mrojas36/CoCoSwitchboard/CoCo1Switchboard/Photos/Capture.PNG

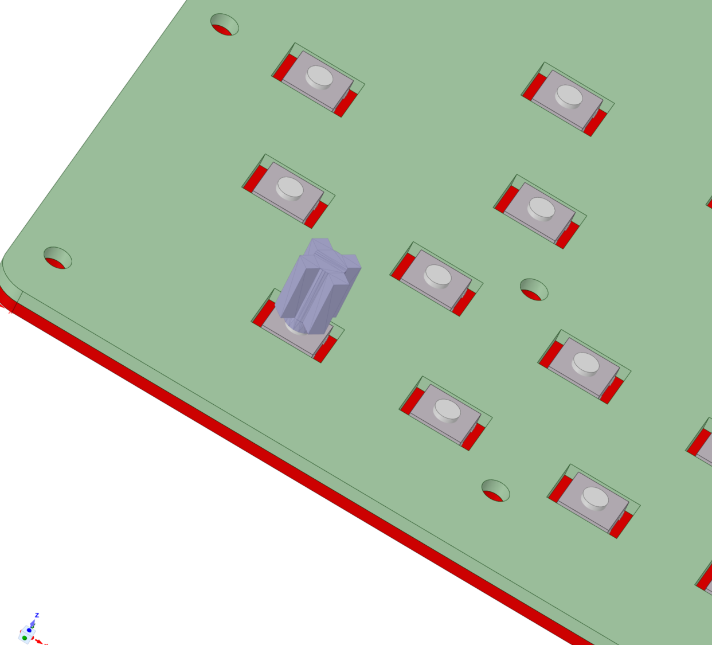
CoCo1Switchboard/Photos/Capture.PNG
