mrojas36/CoCoSwitchboard/CoCo1Switchboard/Photos/Coco1-Keyboard1 (1).JPEG

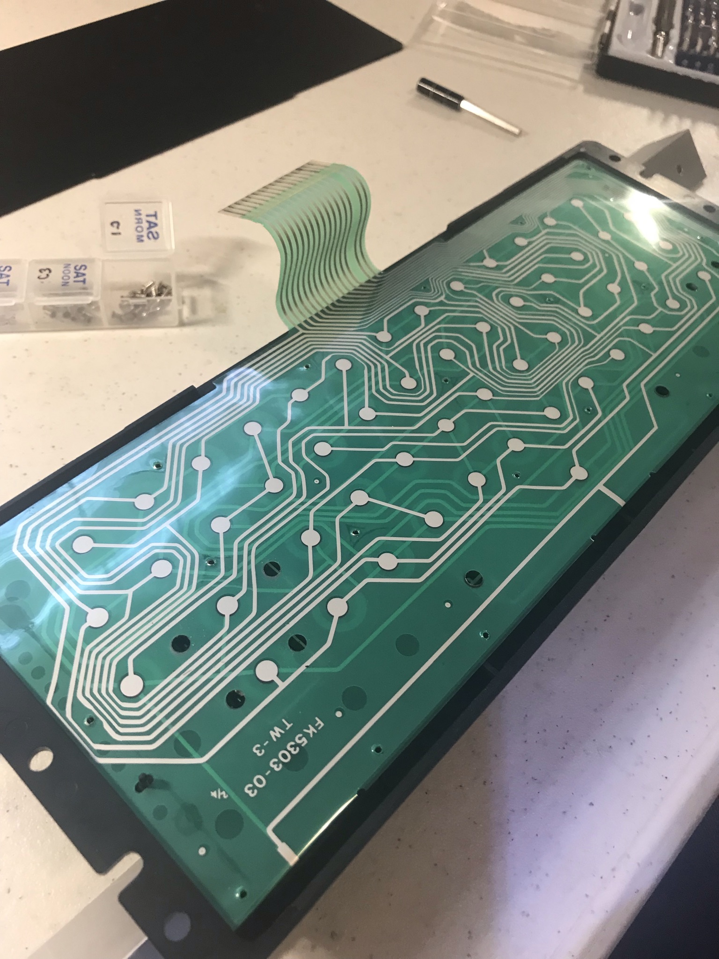
CoCo1Switchboard/Photos/Coco1-Keyboard1 (1).JPEG
