mrojas36/CoCoSwitchboard/CoCo1Switchboard/Photos/Coco1-Keyboard1 (2).JPEG

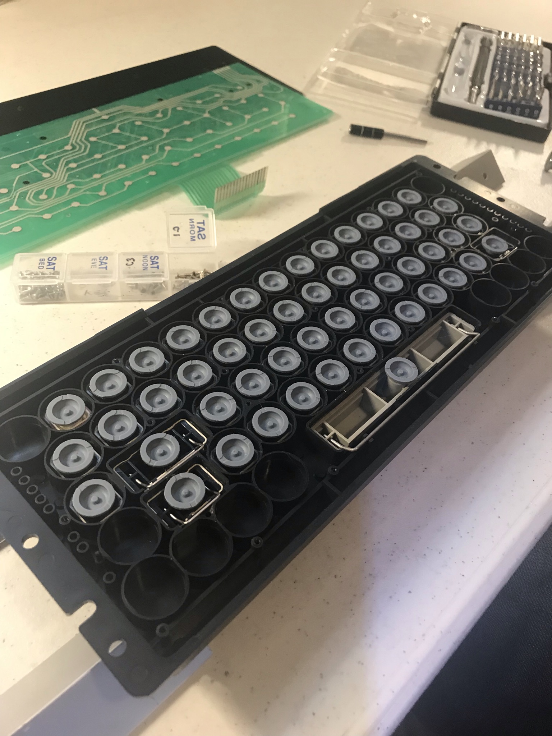
CoCo1Switchboard/Photos/Coco1-Keyboard1 (2).JPEG
