mrojas36/CoCoSwitchboard/CoCo1Switchboard/Photos/IMG_1975.JPEG

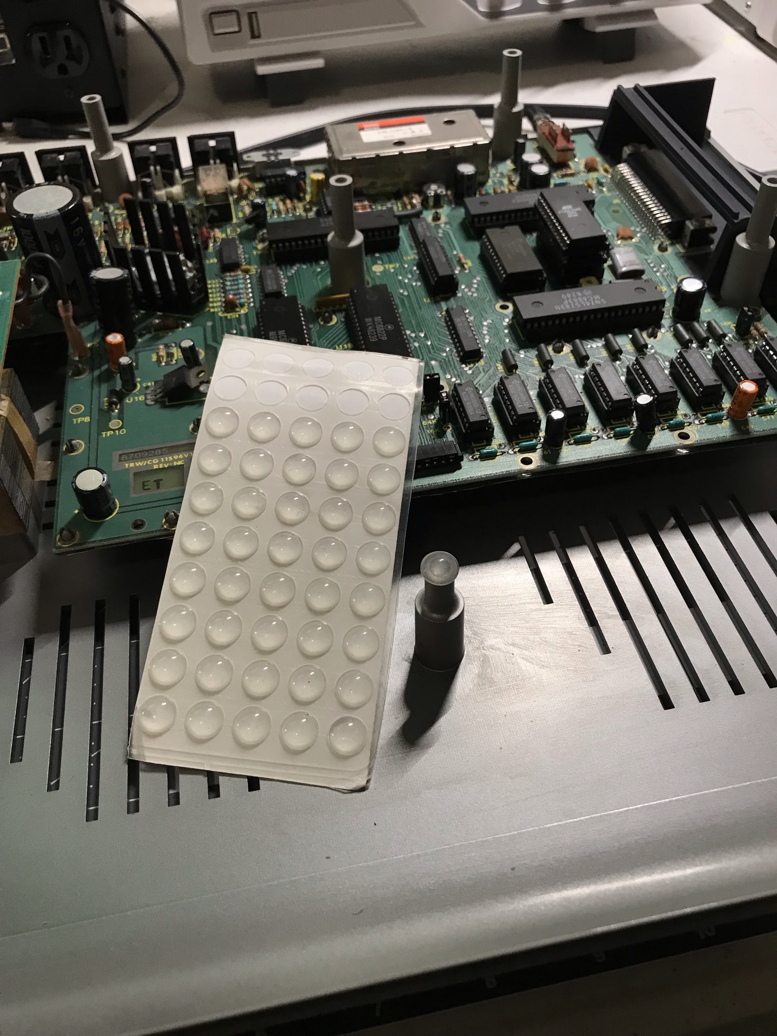
CoCo1Switchboard/Photos/IMG_1975.JPEG
