mrojas36/CoCoSwitchboard/CoCo1Switchboard/Photos/IMG_1976.JPEG

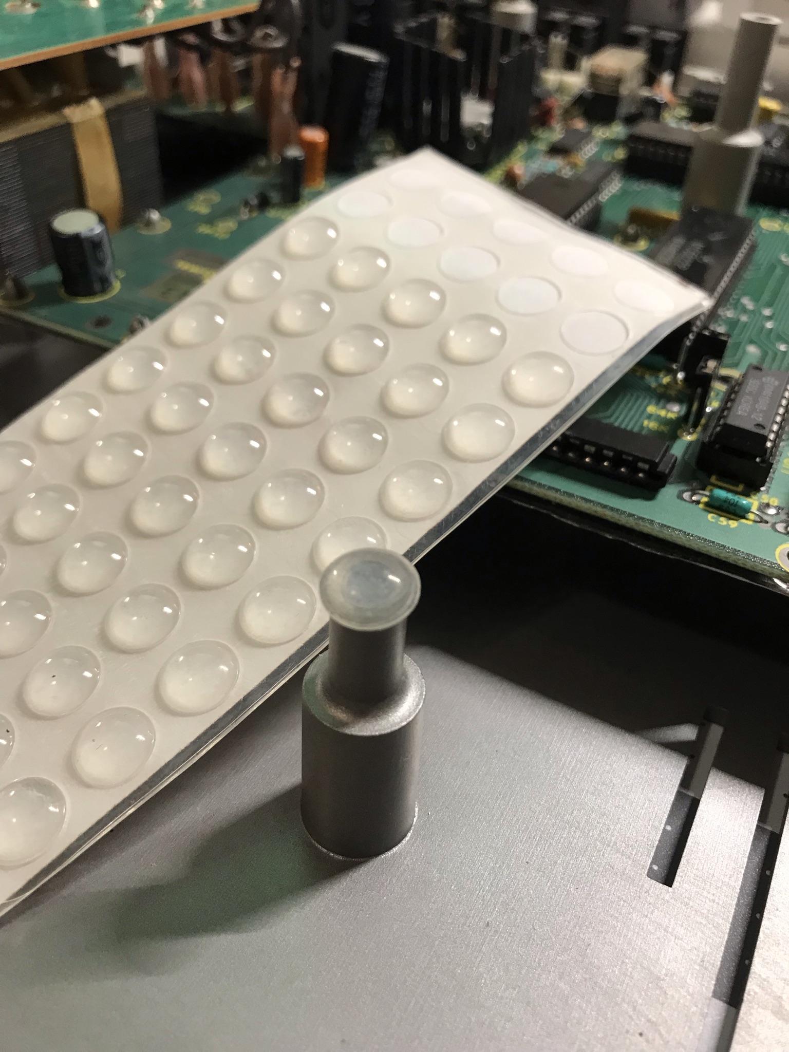
CoCo1Switchboard/Photos/IMG_1976.JPEG
