mrojas36/CoCoSwitchboard/CoCo1Switchboard/Photos/IMG_1977.JPEG

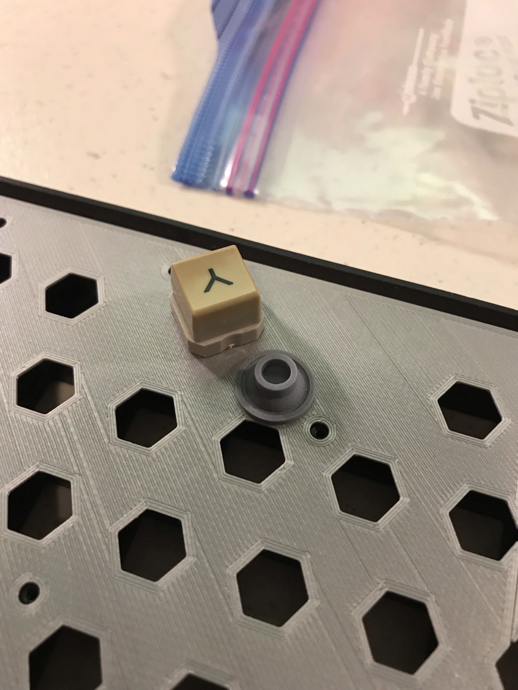
CoCo1Switchboard/Photos/IMG_1977.JPEG
