mrojas36/CoCoSwitchboard/CoCo1Switchboard/Photos/IMG_1978.JPEG

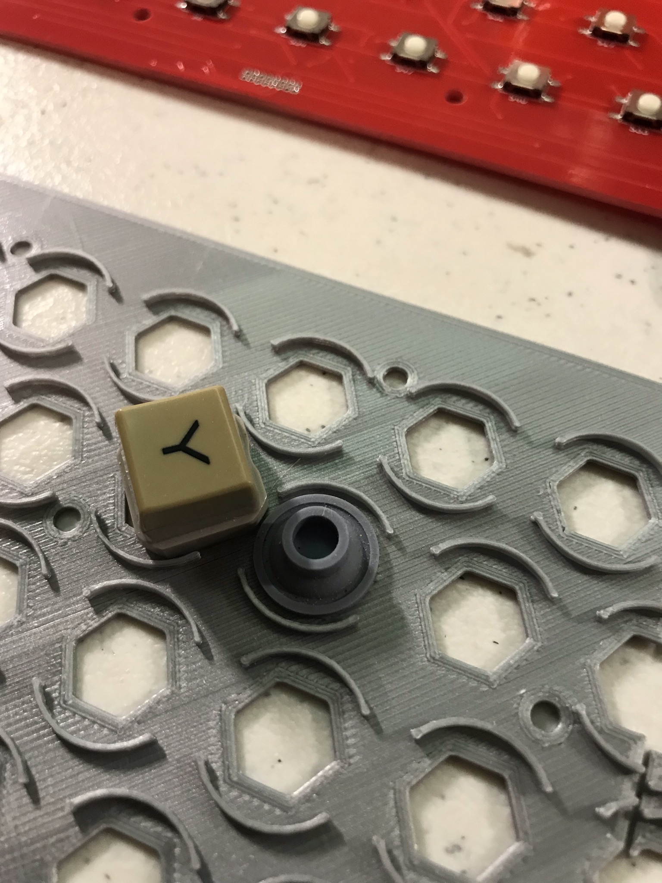
CoCo1Switchboard/Photos/IMG_1978.JPEG
