mrojas36/CoCoSwitchboard/CoCo1Switchboard/Photos/IMG_1979.JPEG

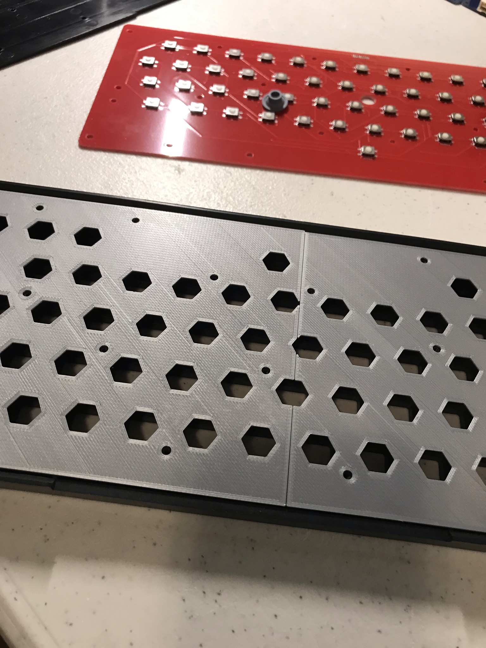
CoCo1Switchboard/Photos/IMG_1979.JPEG
