mrojas36/CoCoSwitchboard/CoCo1Switchboard/Photos/IMG_1980.JPEG

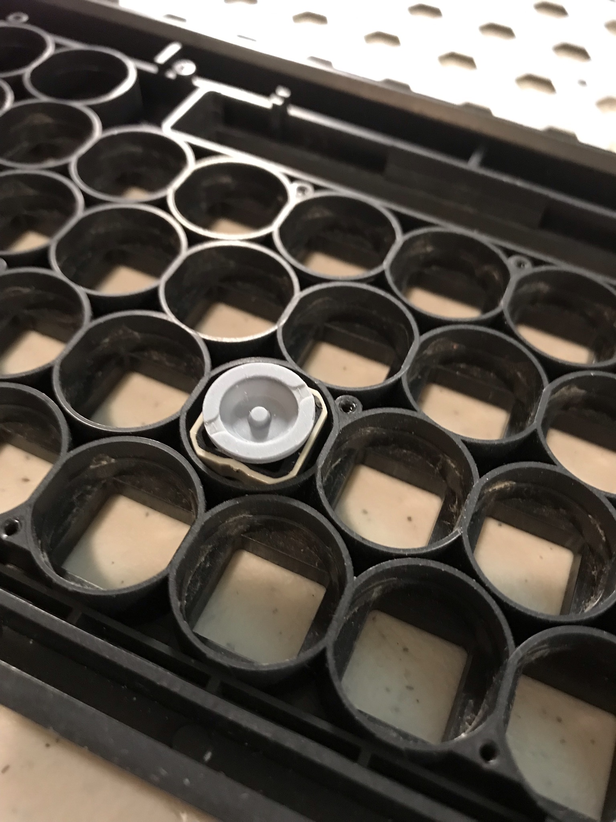
CoCo1Switchboard/Photos/IMG_1980.JPEG
