mrojas36/CoCoSwitchboard/CoCo1Switchboard/Photos/IMG_1981.JPEG

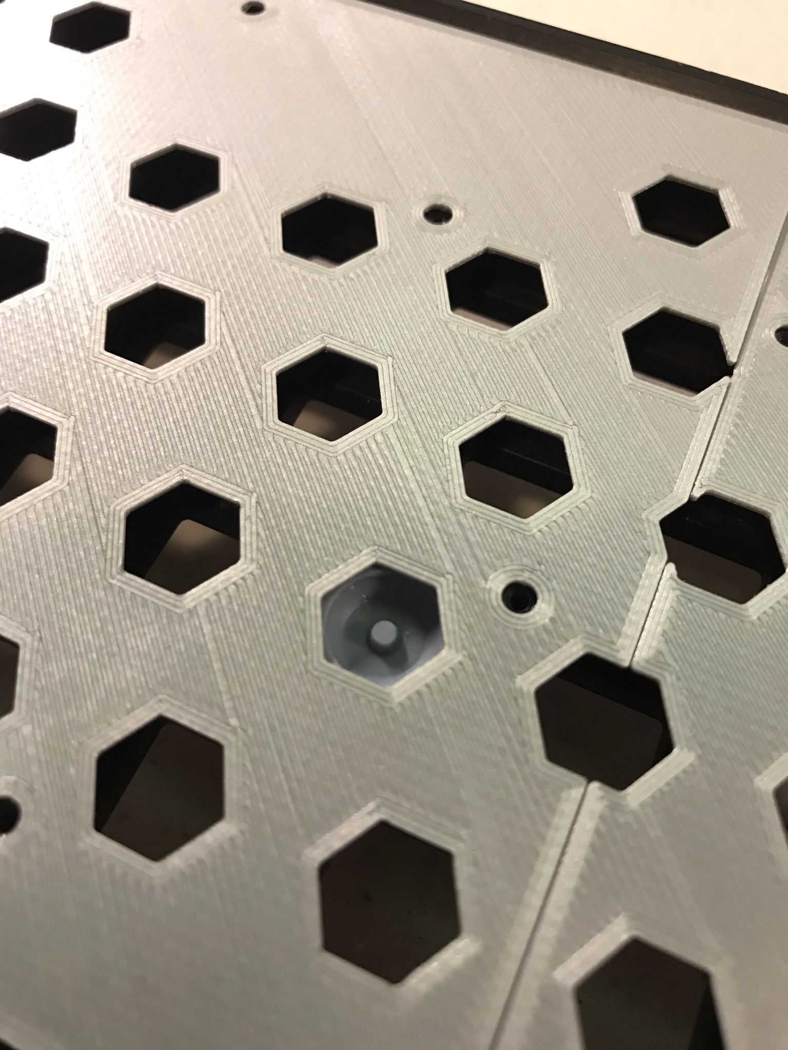
CoCo1Switchboard/Photos/IMG_1981.JPEG
