mrojas36/CoCoSwitchboard/CoCo1Switchboard/Photos/IMG_1982.JPEG

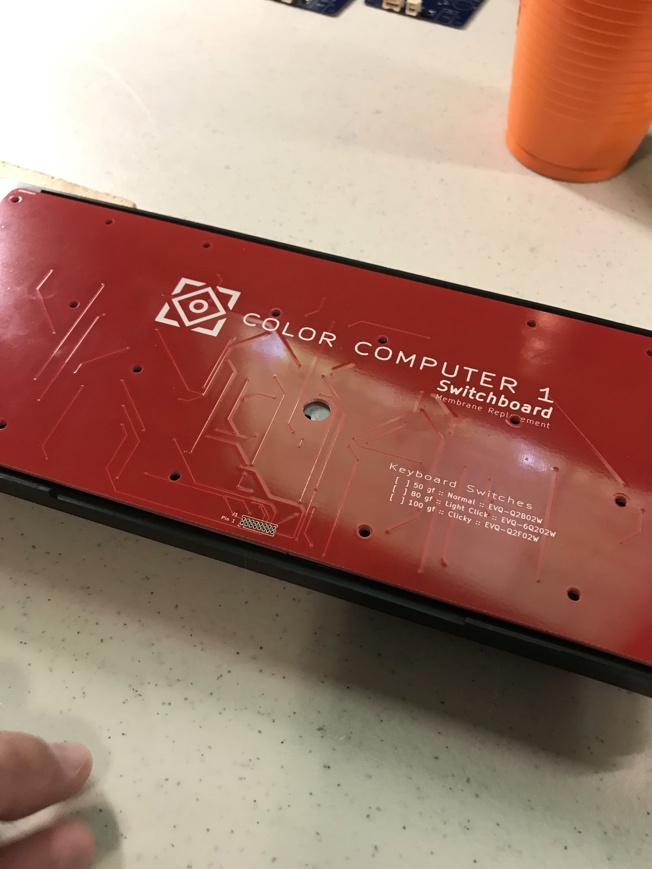
CoCo1Switchboard/Photos/IMG_1982.JPEG
