mrojas36/CoCoSwitchboard/CoCo1Switchboard/Photos/IMG_1983.JPEG

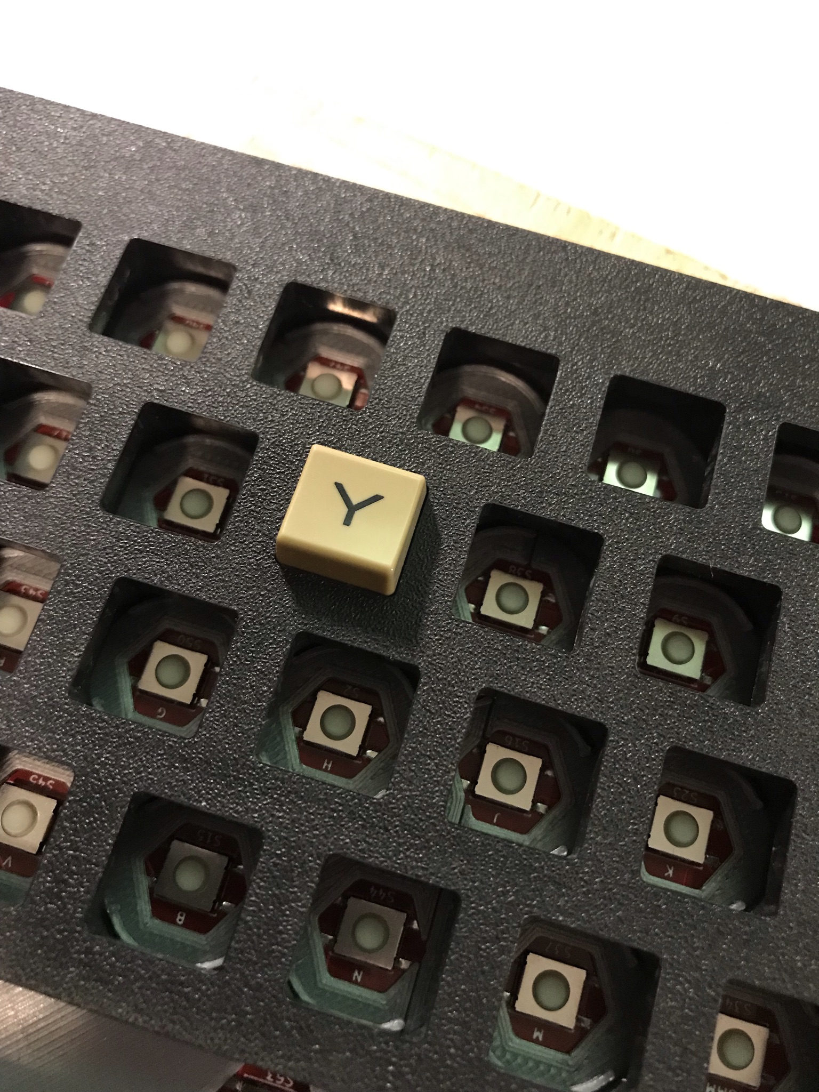
CoCo1Switchboard/Photos/IMG_1983.JPEG
