mrojas36/CoCoSwitchboard/CoCo1Switchboard/Photos/IMG_1984.JPEG

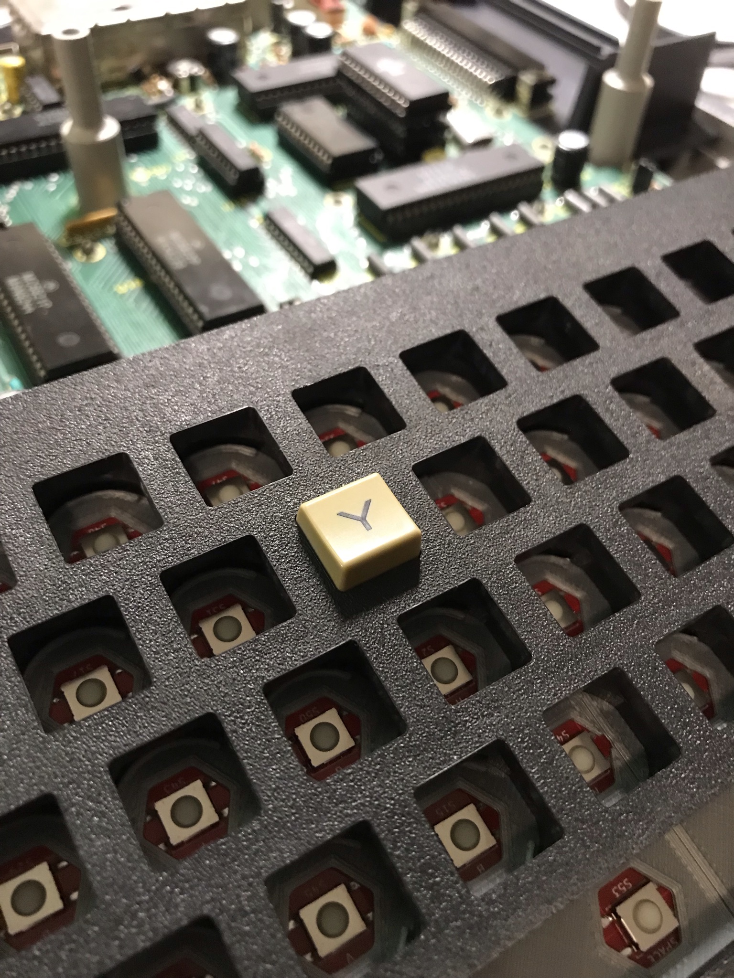
CoCo1Switchboard/Photos/IMG_1984.JPEG
