mrojas36/CoCoSwitchboard/CoCo1Switchboard/Photos/Key1.JPEG

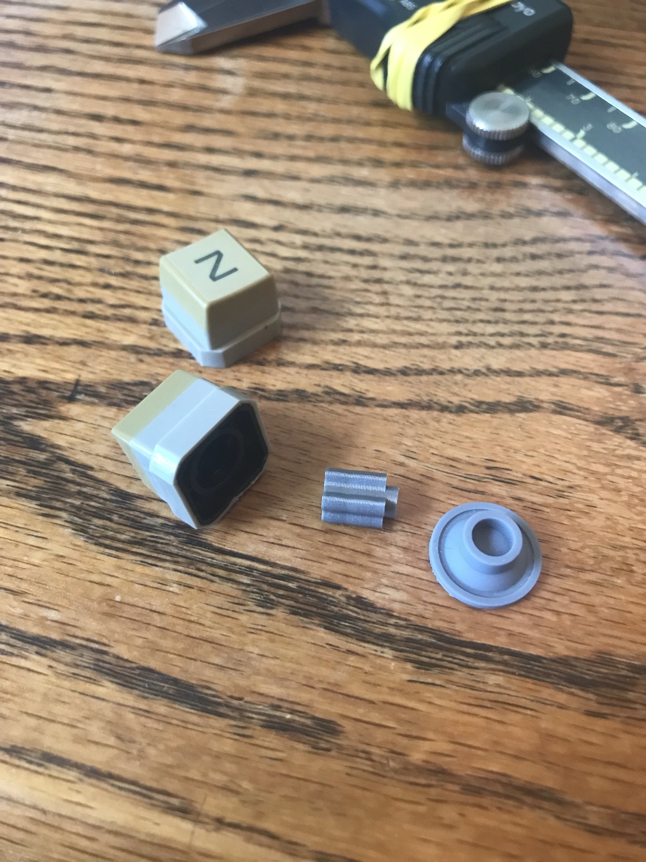
CoCo1Switchboard/Photos/Key1.JPEG
