mrojas36/CoCoSwitchboard/CoCo1Switchboard/Photos/Key2.JPEG

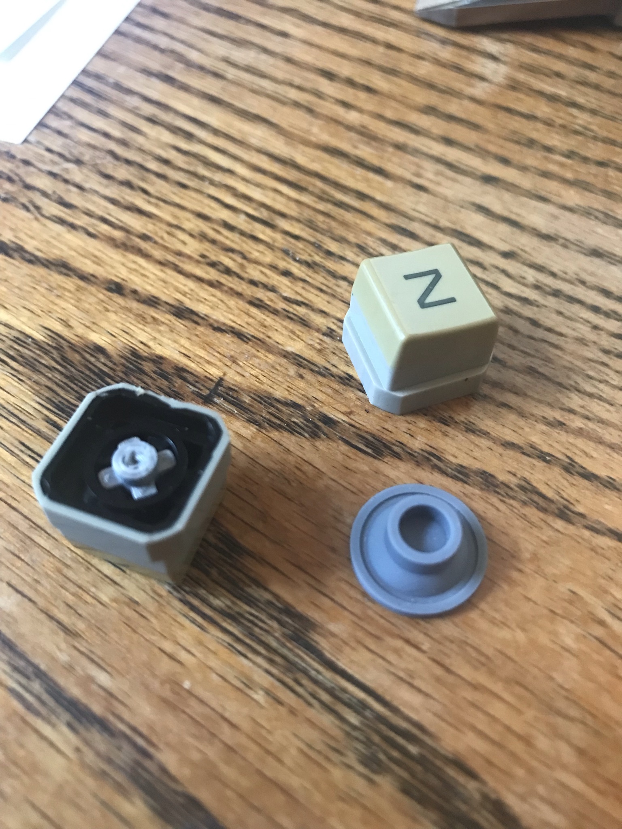
CoCo1Switchboard/Photos/Key2.JPEG
