mrojas36/CoCoSwitchboard/CoCo1Switchboard/Photos/Key3.JPEG

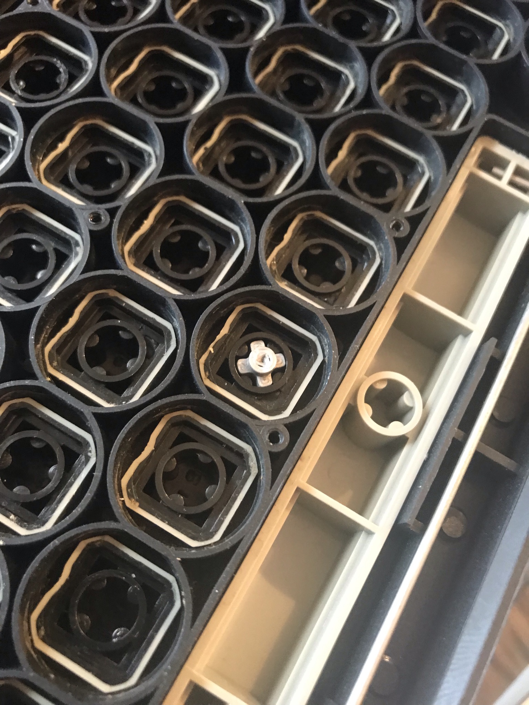
CoCo1Switchboard/Photos/Key3.JPEG
