mrojas36/CoCoSwitchboard/CoCo1Switchboard/Photos/Key4.JPEG

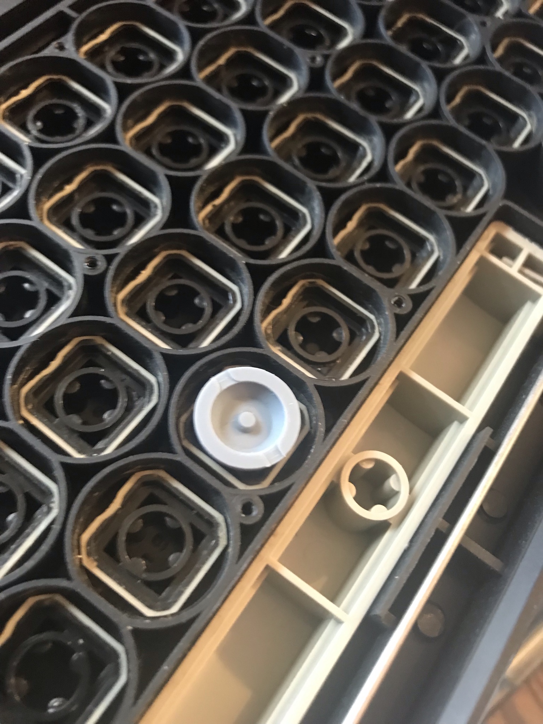
CoCo1Switchboard/Photos/Key4.JPEG
