mrojas36/CoCoSwitchboard/CoCo1Switchboard/Photos/Key-Post-Inserted.PNG

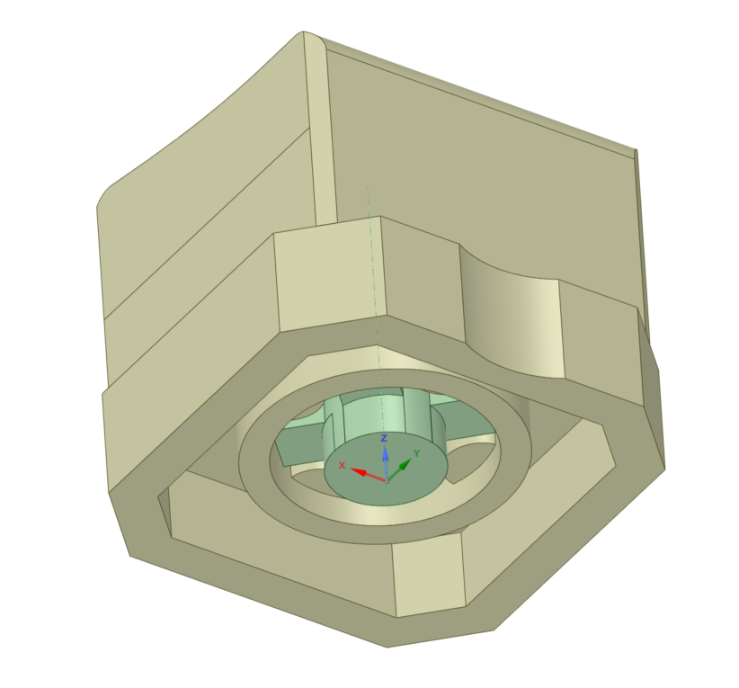
CoCo1Switchboard/Photos/Key-Post-Inserted.PNG
