mrojas36/CoCoSwitchboard/CoCo1Switchboard/Photos/Key-with-Post.png

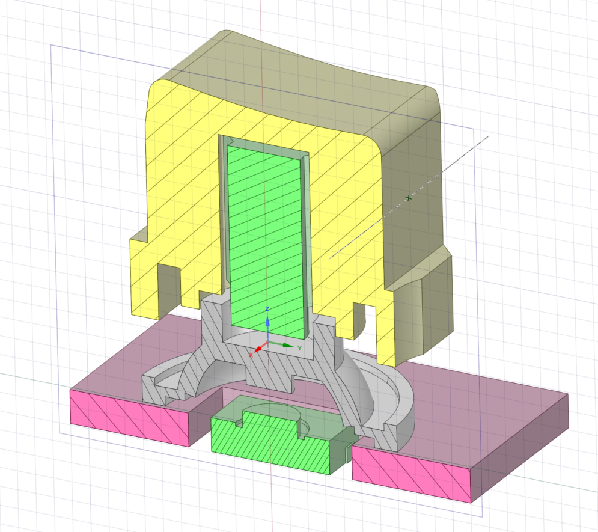
CoCo1Switchboard/Photos/Key-with-Post.png
