mrojas36/CoCoSwitchboard/CoCo1Switchboard/Photos/Key-without-Post.png

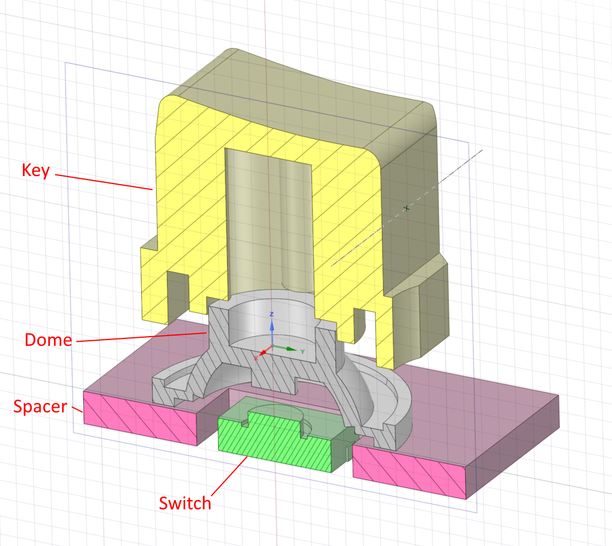
CoCo1Switchboard/Photos/Key-without-Post.png
