mrojas36/CoCoSwitchboard/CoCo2Switchboard/Photos/IMG_1985.JPEG

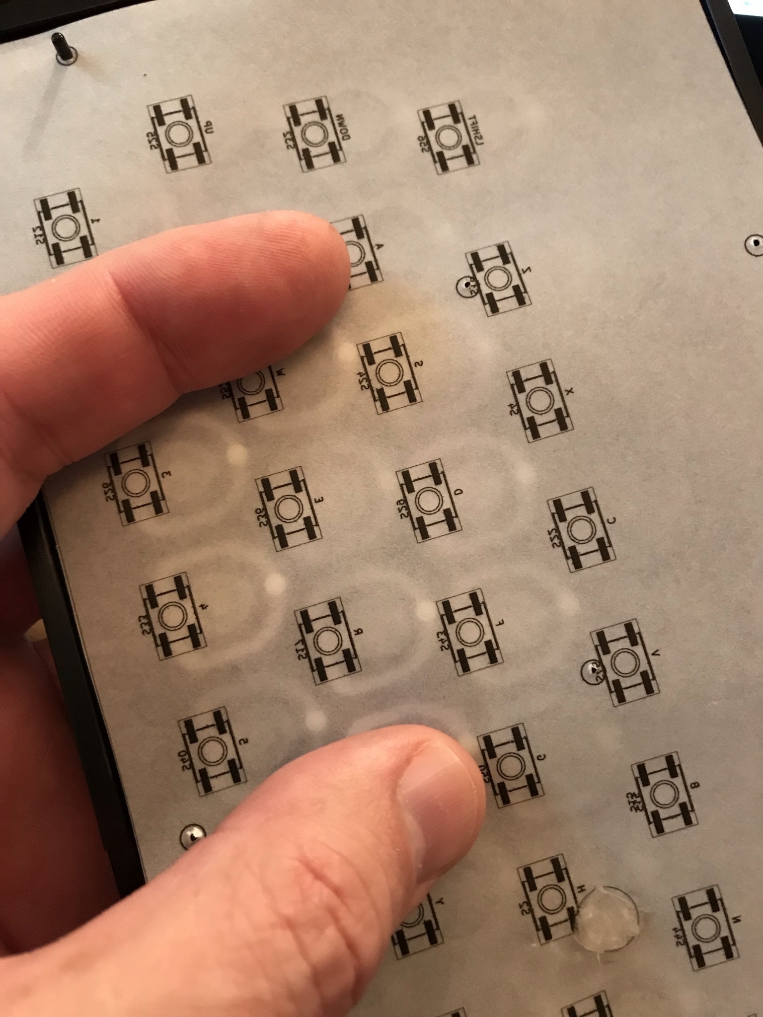
CoCo2Switchboard/Photos/IMG_1985.JPEG
