mrojas36/CoCoSwitchboard/CoCo2Switchboard/Photos/IMG_1986.JPEG

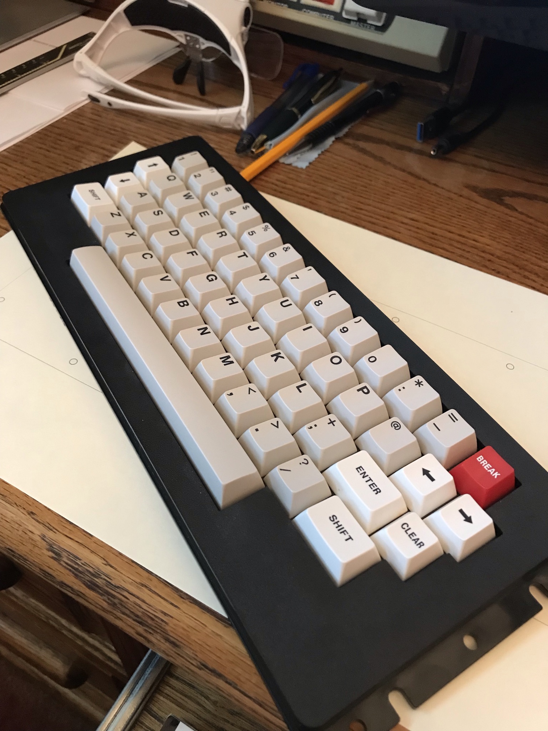
CoCo2Switchboard/Photos/IMG_1986.JPEG
