mrojas36/CoCoSwitchboard/CoCo2Switchboard/Photos/IMG_1987.JPEG

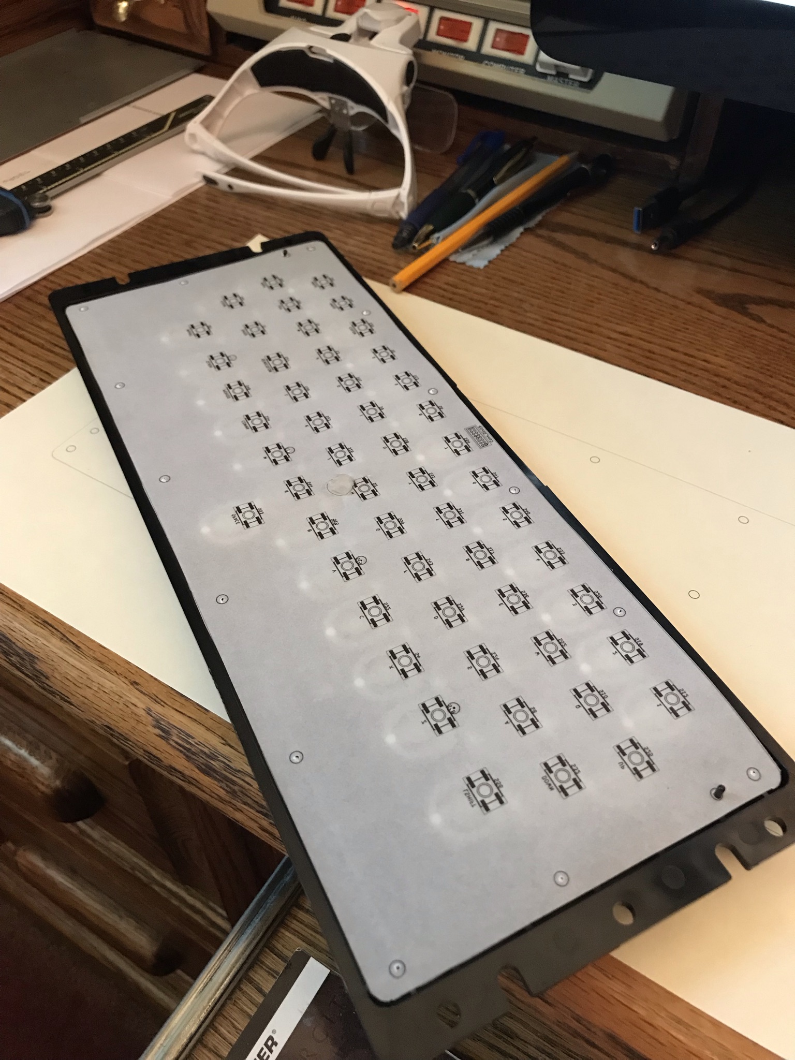
CoCo2Switchboard/Photos/IMG_1987.JPEG
