mrojas36/CoCoSwitchboard/CoCo2Switchboard/Photos/Kicad-Layout.PNG

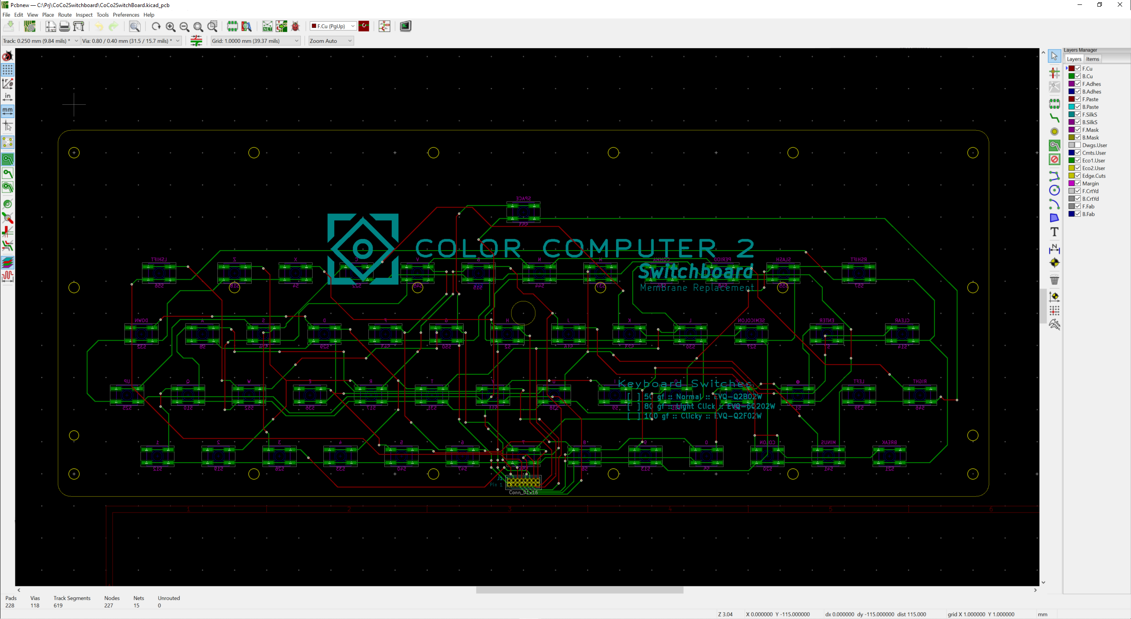
CoCo2Switchboard/Photos/Kicad-Layout.PNG
