mrojas36/CoCoSwitchboard/CoCo2Switchboard/Photos/Updated-Spacer-Lighter-Feel-Closeup.PNG

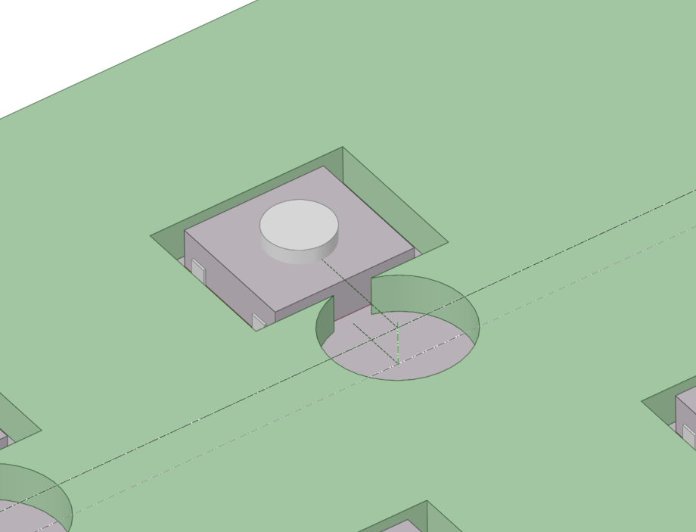
CoCo2Switchboard/Photos/Updated-Spacer-Lighter-Feel-Closeup.PNG
