mrojas36/CoCoSwitchboard/CoCo2Switchboard/Photos/Updated-Spacer-Lighter-Feel.PNG

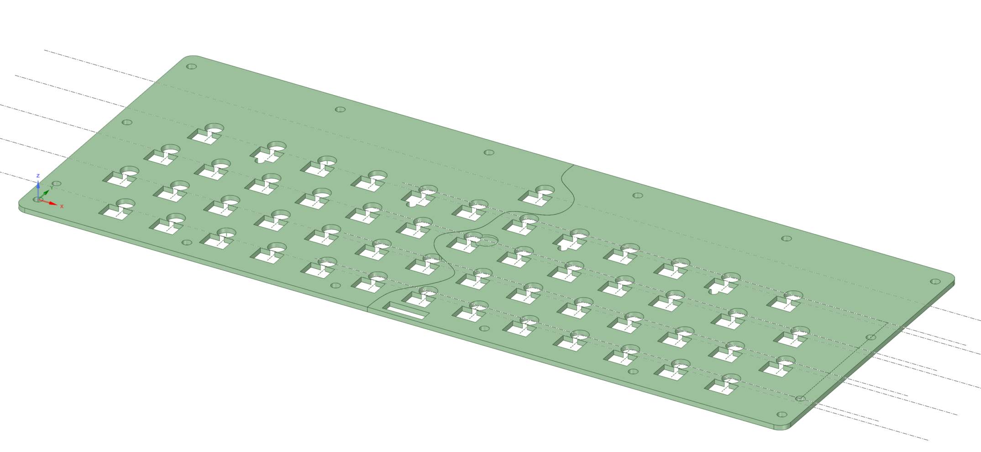
CoCo2Switchboard/Photos/Updated-Spacer-Lighter-Feel.PNG
