mrojas36/CoCoSwitchboard/CoCo3Switchboard/Photos/CoCo3SwitchBoard3.png

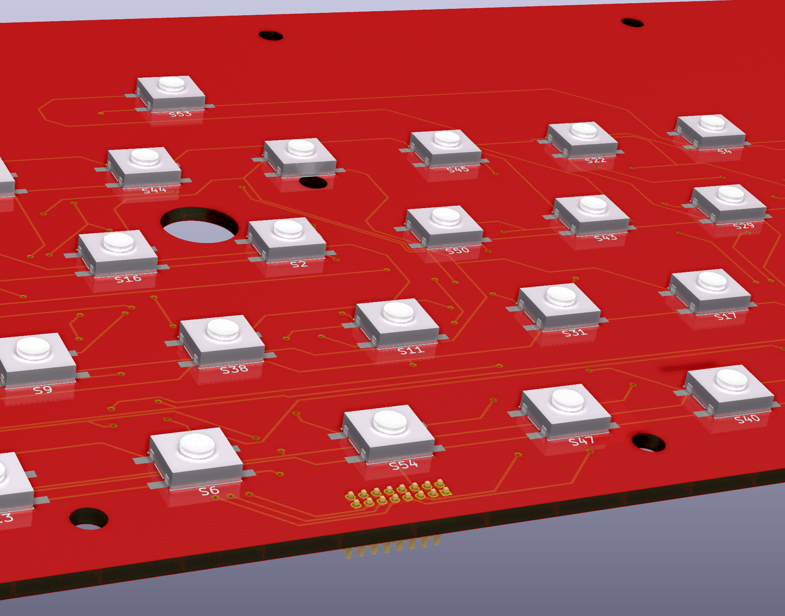
CoCo3Switchboard/Photos/CoCo3SwitchBoard3.png
