mrojas36/CoCoSwitchboard/CoCo3Switchboard/Photos/CoCo3SwitchBoard5.png

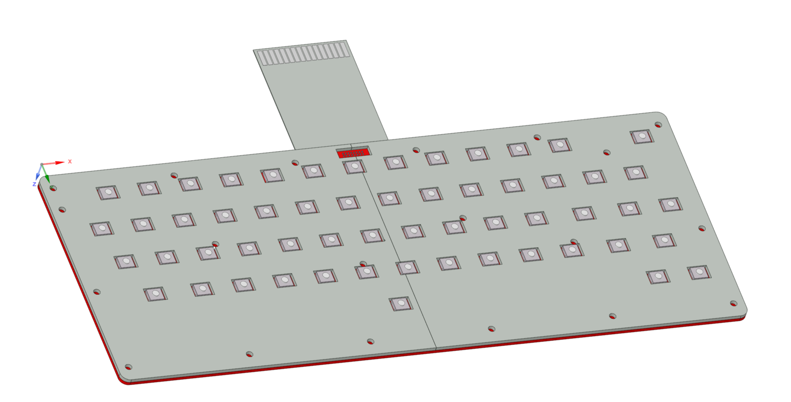
CoCo3Switchboard/Photos/CoCo3SwitchBoard5.png
