mrojas36/CoCoSwitchboard/CoCo3Switchboard/Photos/CoCo3SwitchBoard6.png

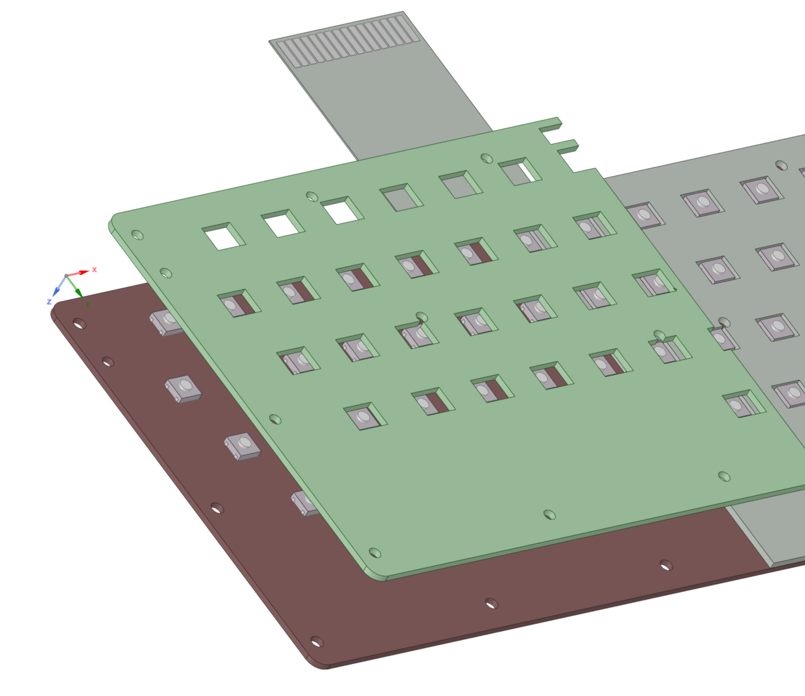
CoCo3Switchboard/Photos/CoCo3SwitchBoard6.png
