mrojas36/CoCoSwitchboard/CoCo3Switchboard/Photos/CoCo3SwitchBoard8.png

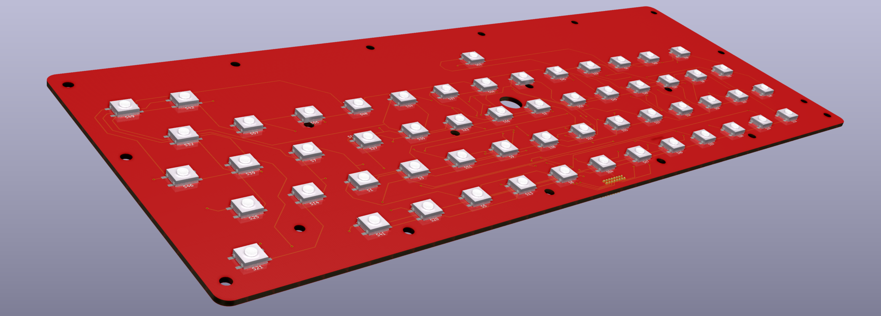
CoCo3Switchboard/Photos/CoCo3SwitchBoard8.png
