mrojas36/CoCoSwitchboard/CoCo3Switchboard/Photos/CoCo3SwitchBoard.png

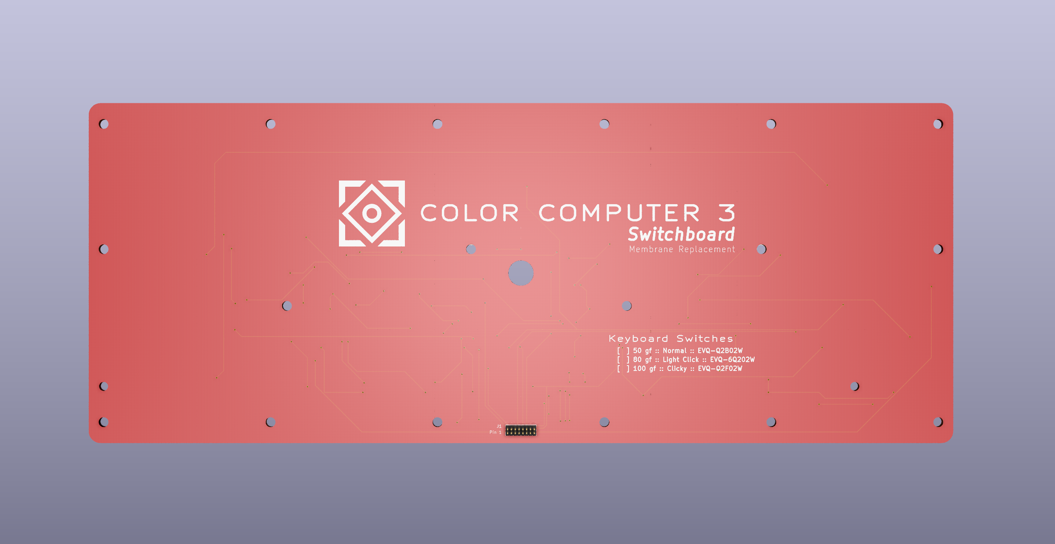
CoCo3Switchboard/Photos/CoCo3SwitchBoard.png
