mrojas36/CoCoSwitchboard/CoCo3Switchboard/Photos/Jib2.JPG

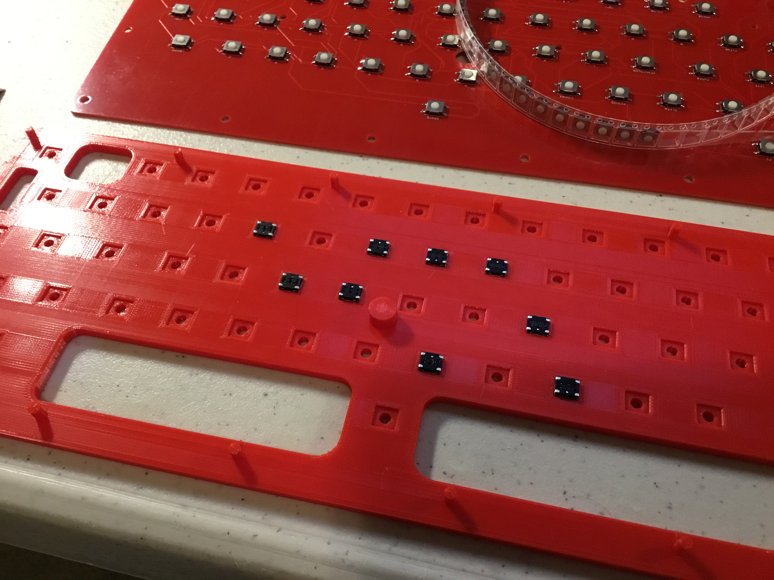
CoCo3Switchboard/Photos/Jib2.JPG
