mrojas36/CoCoSwitchboard/CoCo3Switchboard/Photos/Jib4.JPG

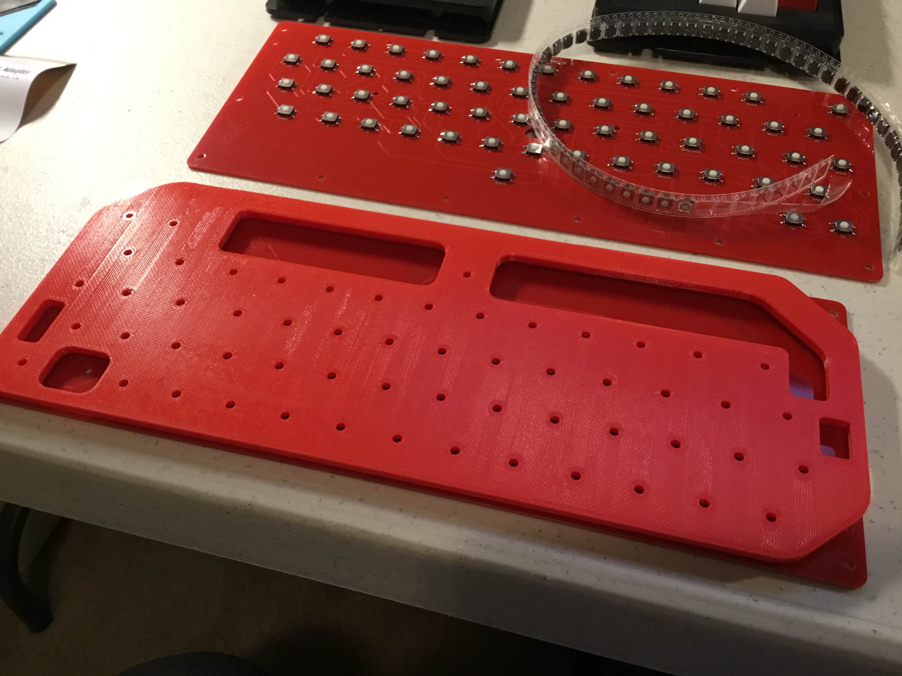
CoCo3Switchboard/Photos/Jib4.JPG
