mrojas36/CoCoSwitchboard/CoCo3Switchboard/Photos/Jib5.JPG

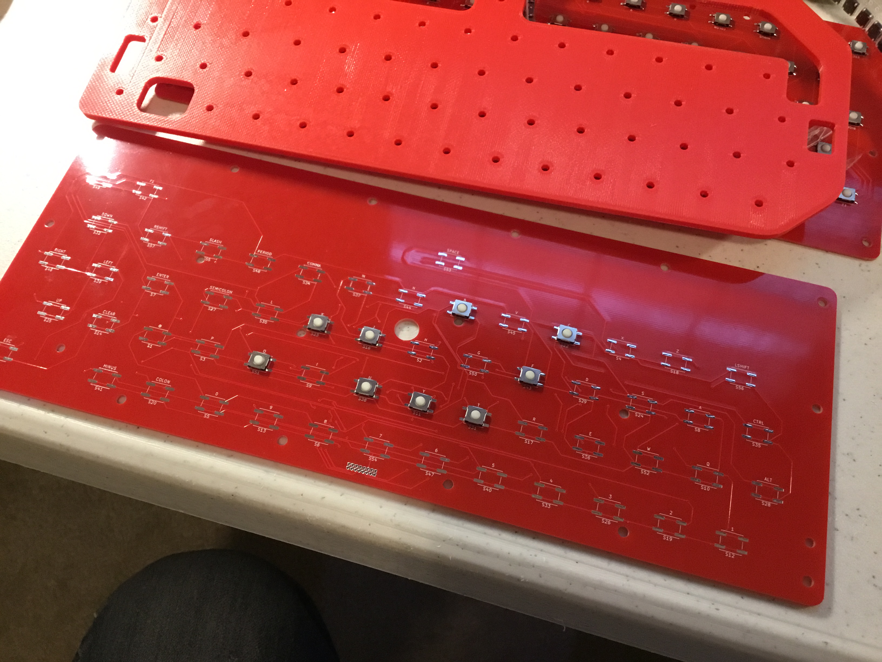
CoCo3Switchboard/Photos/Jib5.JPG
