mrojas36/CoCoSwitchboard/CoCo3Switchboard/Photos/Jib.PNG

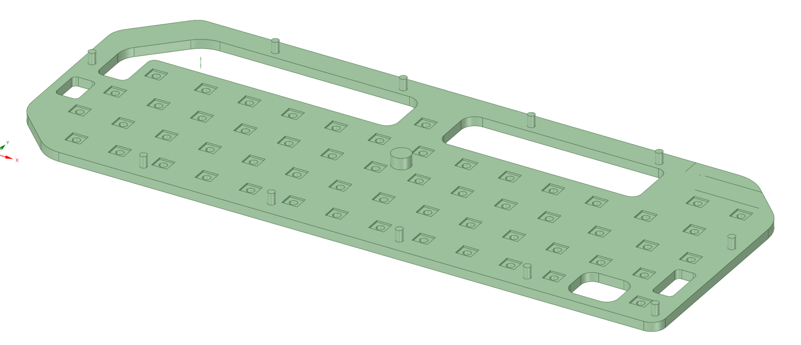
CoCo3Switchboard/Photos/Jib.PNG
