mrojas36/CoCoSwitchboard/CoCo3Switchboard/Photos/Jig1.JPG

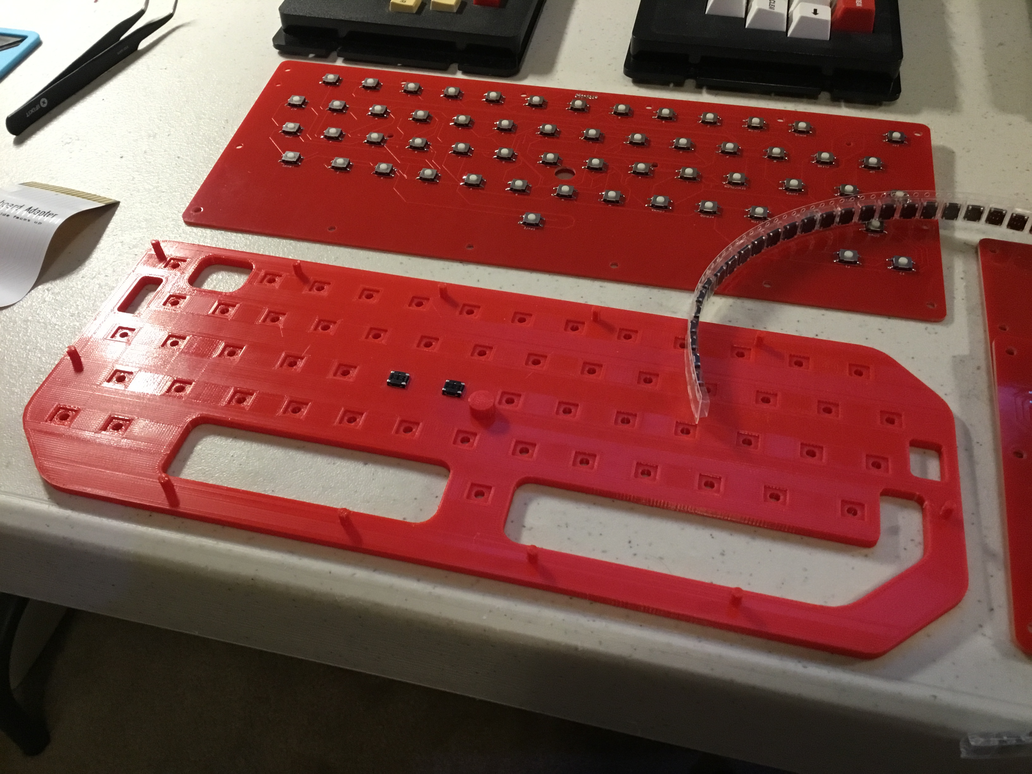
CoCo3Switchboard/Photos/Jig1.JPG
