mrojas36/CoCoSwitchboard/CoCo3Switchboard/Photos/Keyboards.JPG

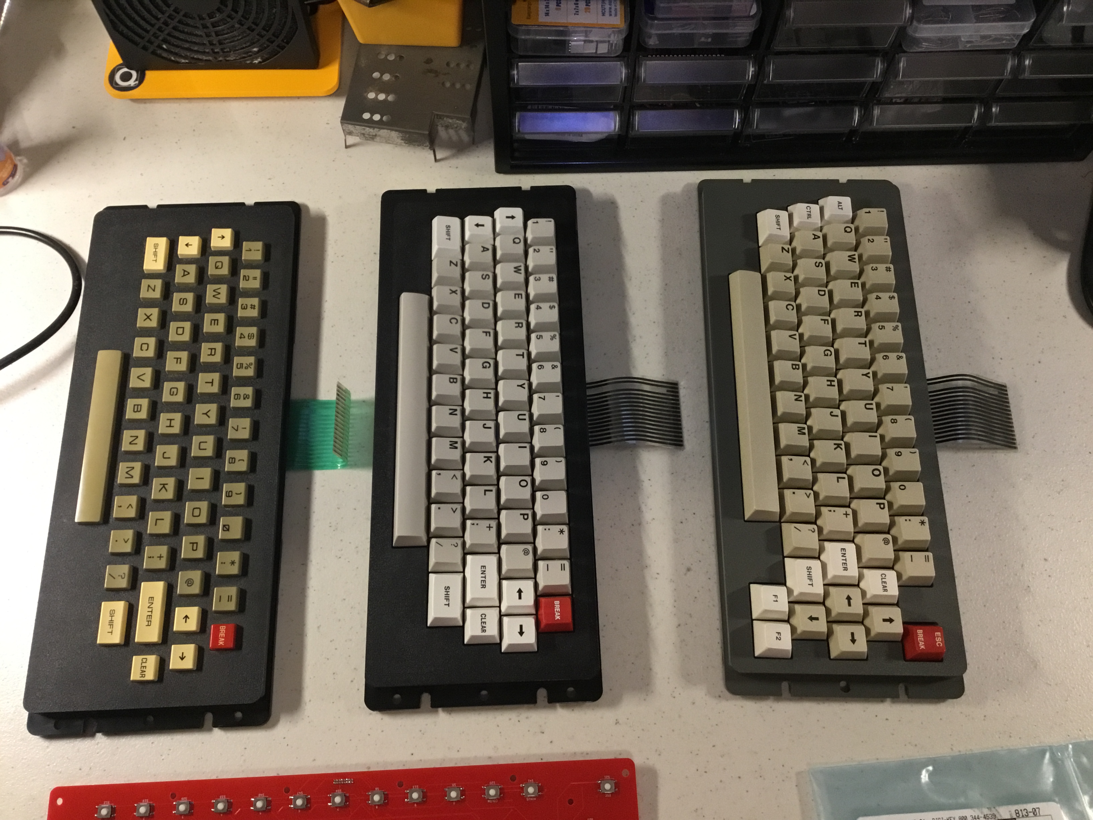
CoCo3Switchboard/Photos/Keyboards.JPG
