mrojas36/CoCoSwitchboard/CoCo3Switchboard/Photos/KeyboardStrike.png

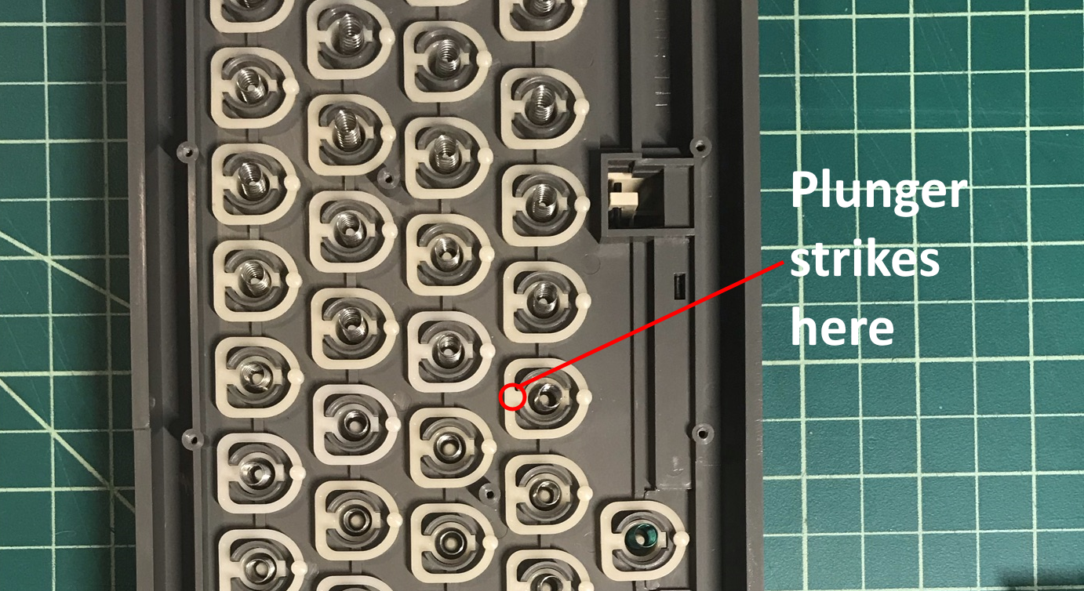
CoCo3Switchboard/Photos/KeyboardStrike.png
