mrojas36/CoCoSwitchboard/CoCo3Switchboard/Photos/Reflow1.JPG

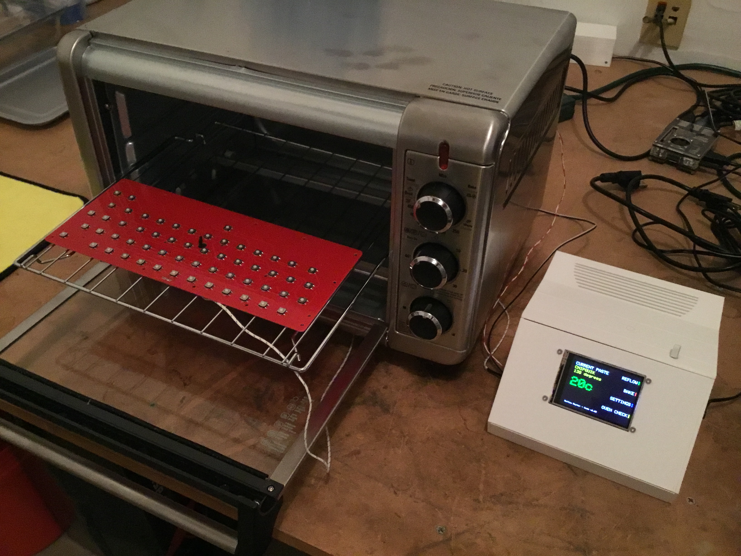
CoCo3Switchboard/Photos/Reflow1.JPG
