mrojas36/CoCoSwitchboard/CoCo3Switchboard/Photos/Reflow2.JPG

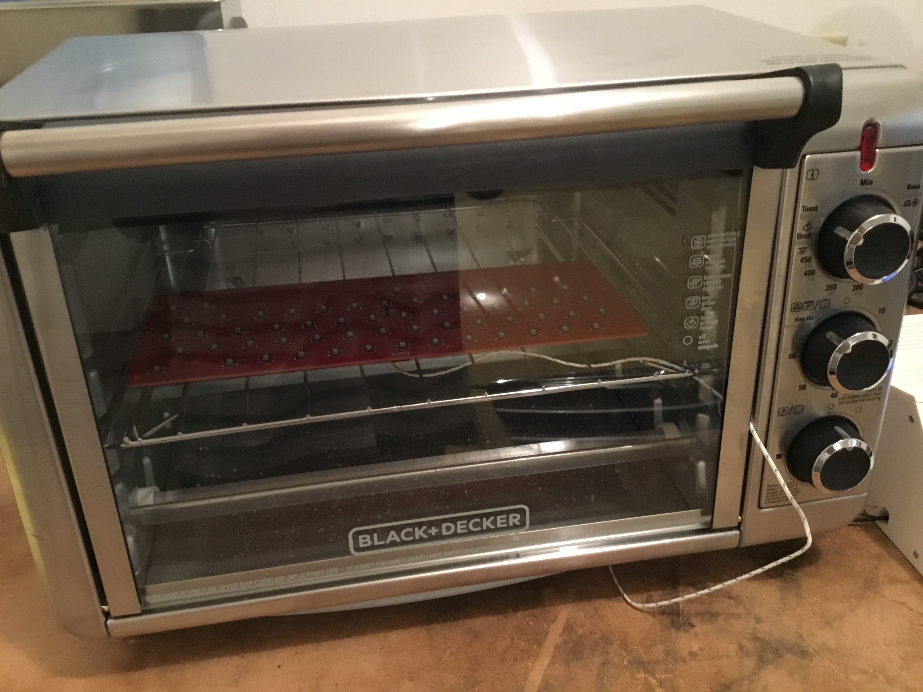
CoCo3Switchboard/Photos/Reflow2.JPG
