mrojas36/CoCoSwitchboard/CoCo3Switchboard/Photos/Reflow3.JPG

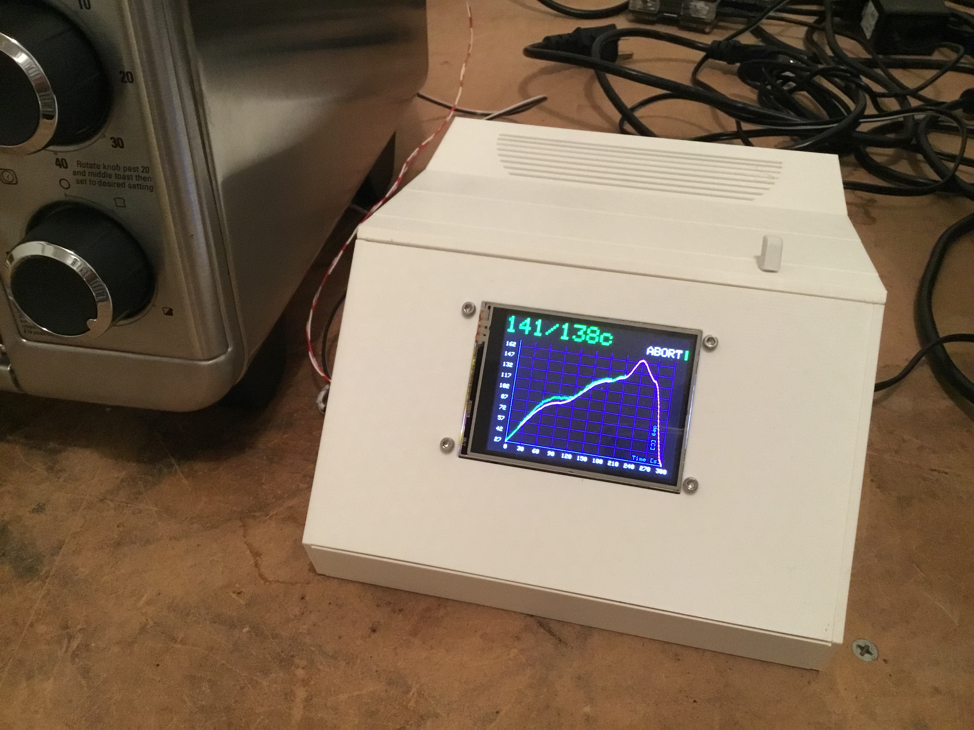
CoCo3Switchboard/Photos/Reflow3.JPG
