mrojas36/CoCoSwitchboard/CoCo3Switchboard/Photos/Reflow4.JPG

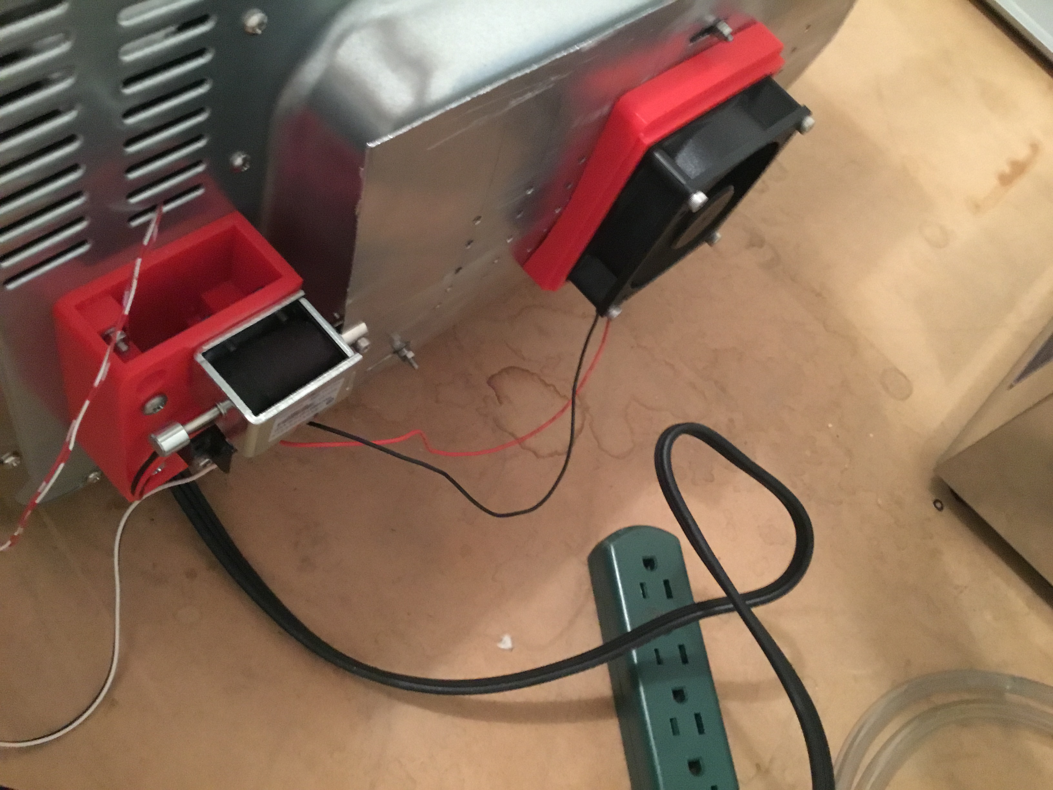
CoCo3Switchboard/Photos/Reflow4.JPG
