mrojas36/CoCoSwitchboard/CoCo3Switchboard/Photos/Reflow5.JPG

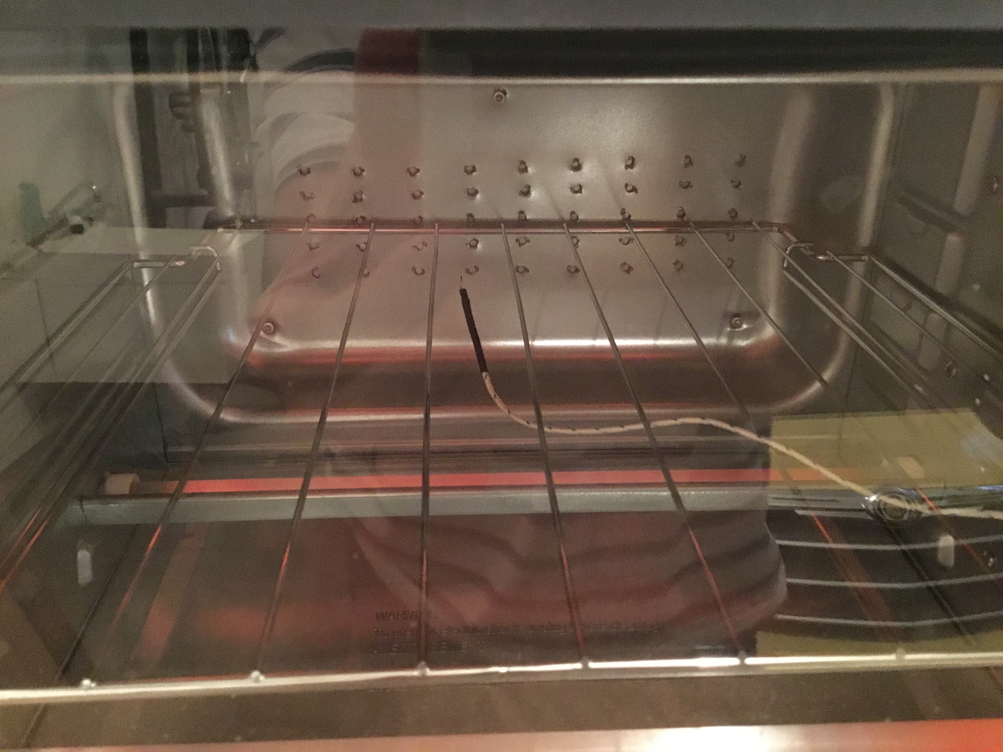
CoCo3Switchboard/Photos/Reflow5.JPG
