mrojas36/CoCoSwitchboard/CoCo3Switchboard/Photos/Reflow6.JPG

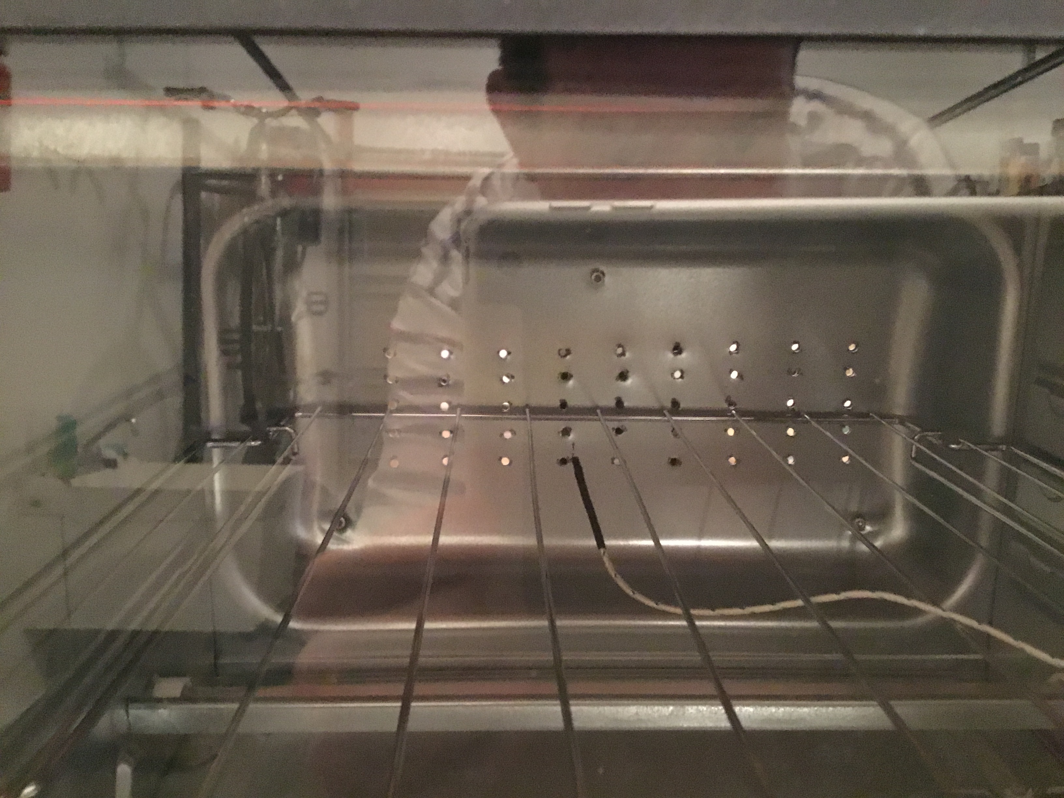
CoCo3Switchboard/Photos/Reflow6.JPG
