mrojas36/CoCoSwitchboard/KBAdapter/Output/KBAdapter-Stiffener.PNG

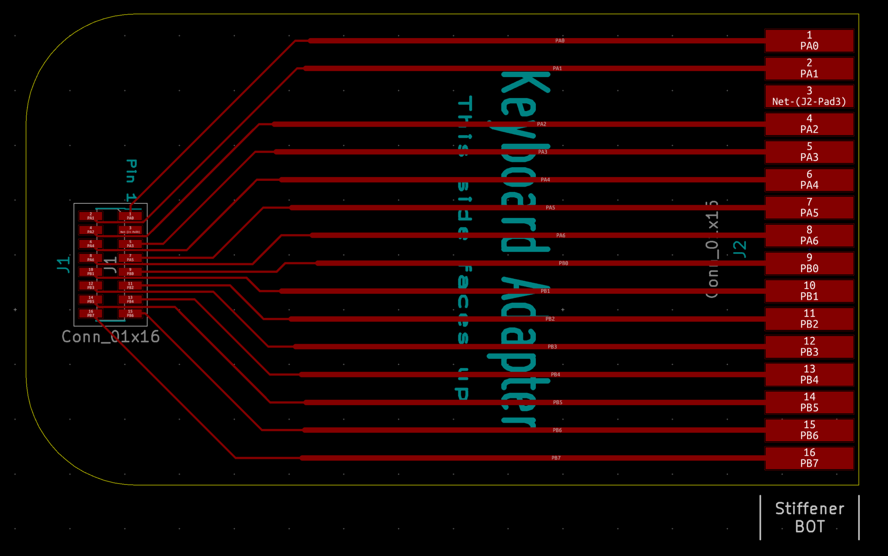
KBAdapter/Output/KBAdapter-Stiffener.PNG
