mrojas36/CoCoSwitchboard/KBAdapter/Photos/IMG_1994.JPEG

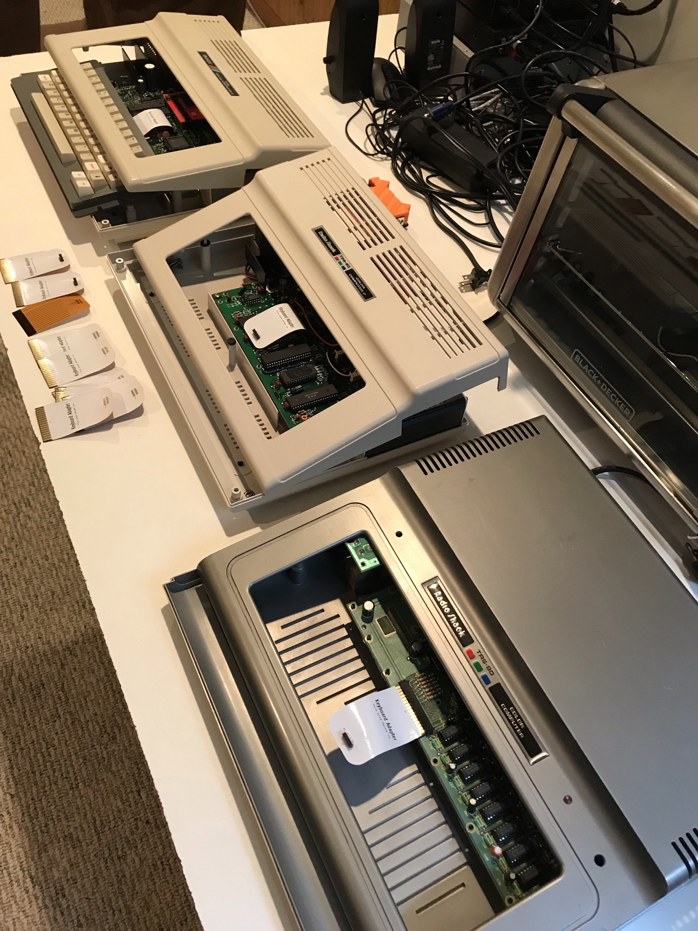
KBAdapter/Photos/IMG_1994.JPEG
