mrojas36/CoCoSwitchboard/KBAdapter/Photos/IMG_1995.JPEG

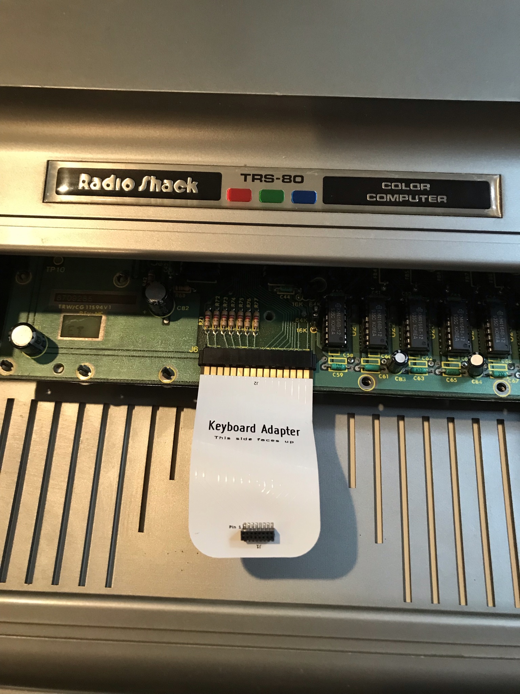
KBAdapter/Photos/IMG_1995.JPEG
