mrojas36/CoCoSwitchboard/KBAdapter/Photos/IMG_1996.JPEG

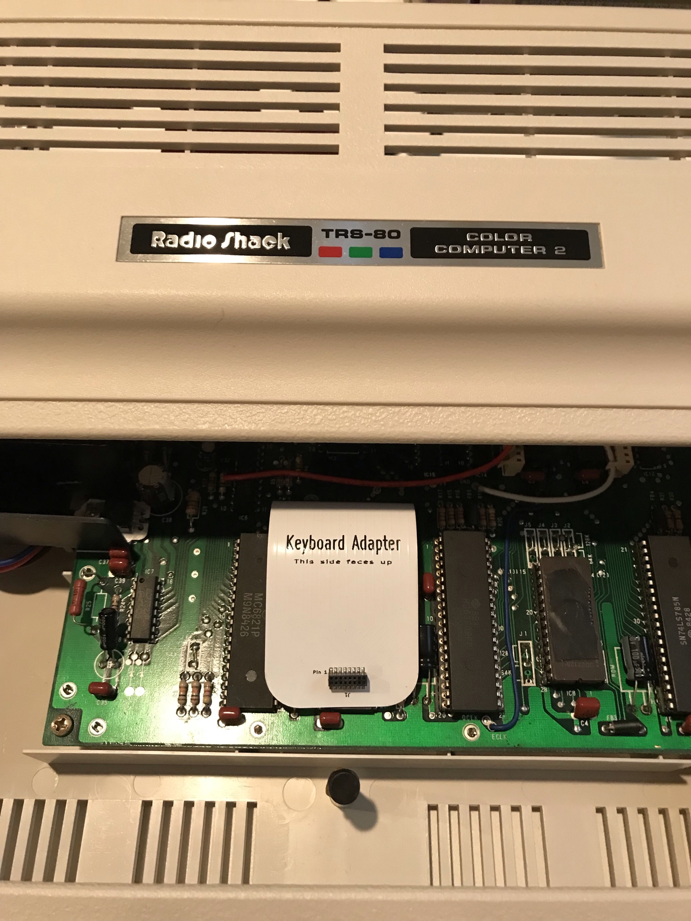
KBAdapter/Photos/IMG_1996.JPEG
