mrojas36/CoCoSwitchboard/KBAdapter/Photos/IMG_1997.JPEG

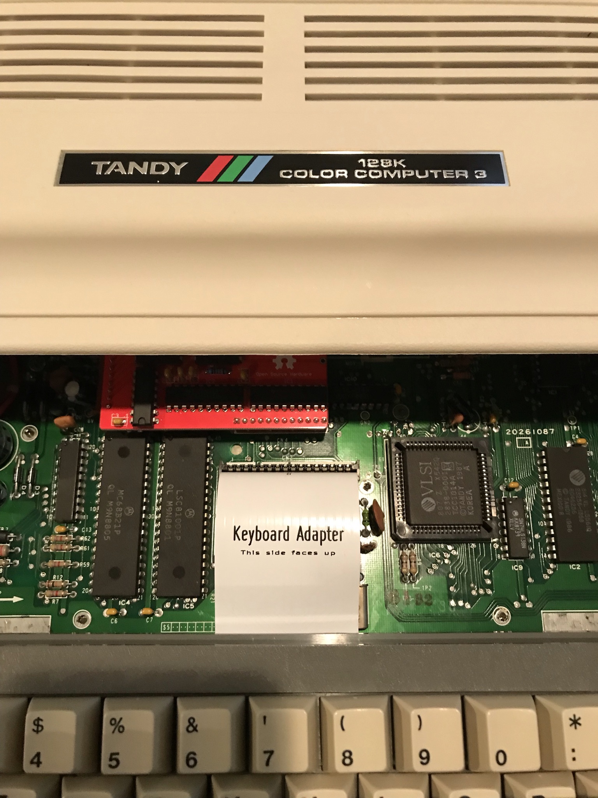
KBAdapter/Photos/IMG_1997.JPEG
