mrojas36/CoCoSwitchboard/KBAdapter/Photos/IMG_1998.JPEG

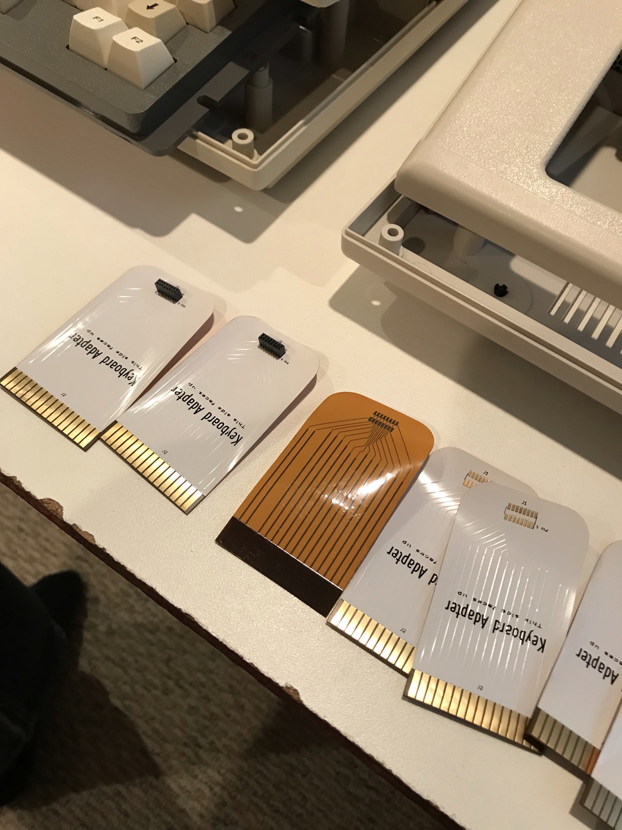
KBAdapter/Photos/IMG_1998.JPEG
