mrojas36/CoCoSwitchboard/KBAdapter/Photos/IMG_1999.JPEG

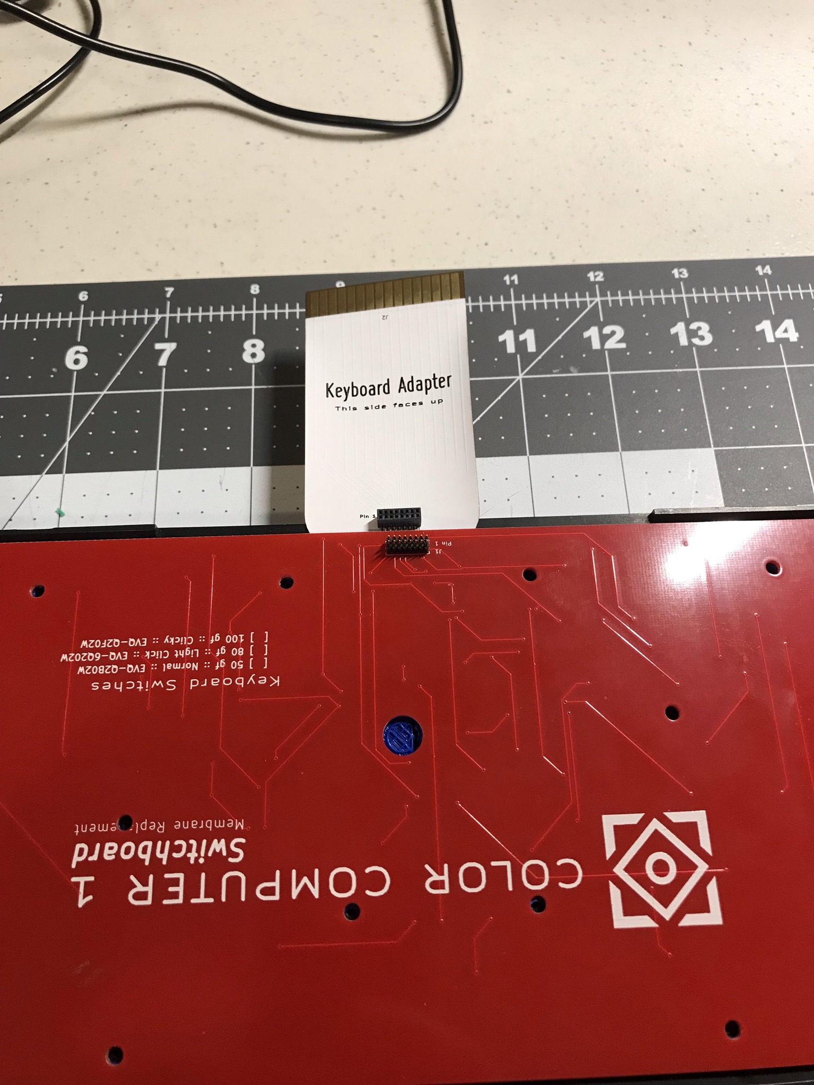
KBAdapter/Photos/IMG_1999.JPEG
