mrojas36/CoCoSwitchboard/KBAdapter/Photos/IMG_2001.JPEG

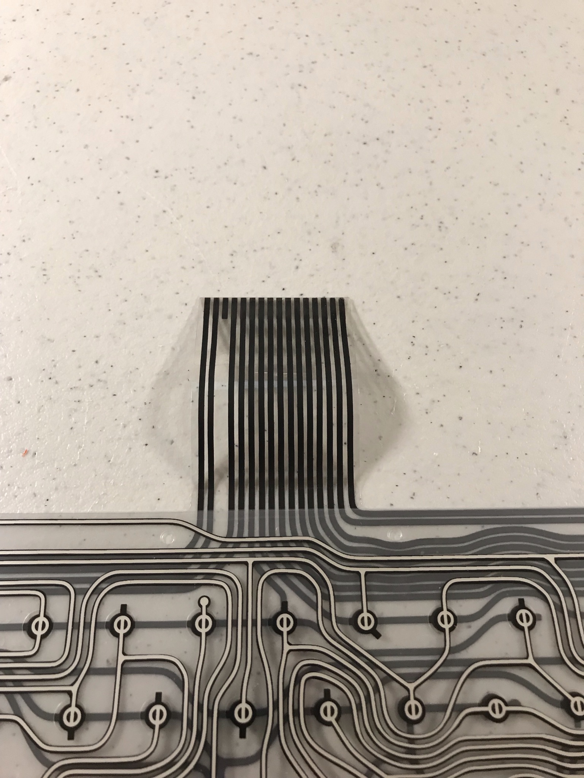
KBAdapter/Photos/IMG_2001.JPEG
