mrojas36/CoCoSwitchboard/KBAdapter/Photos/IMG_2002.JPEG

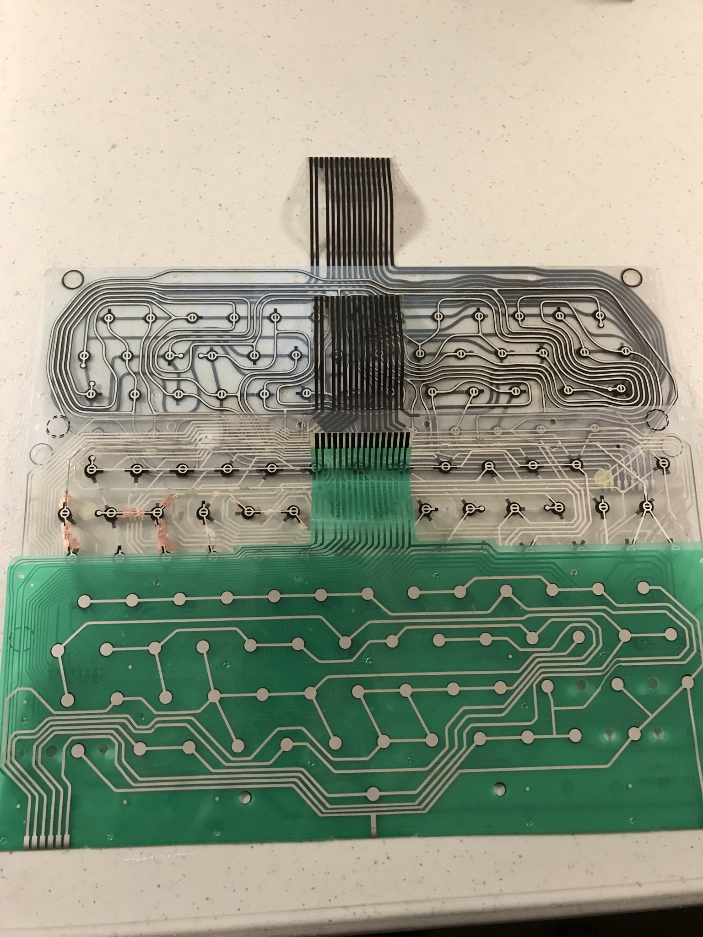
KBAdapter/Photos/IMG_2002.JPEG
