mrojas36/CoCoSwitchboard/KBAdapter/Photos/Kicad-Adapter.PNG

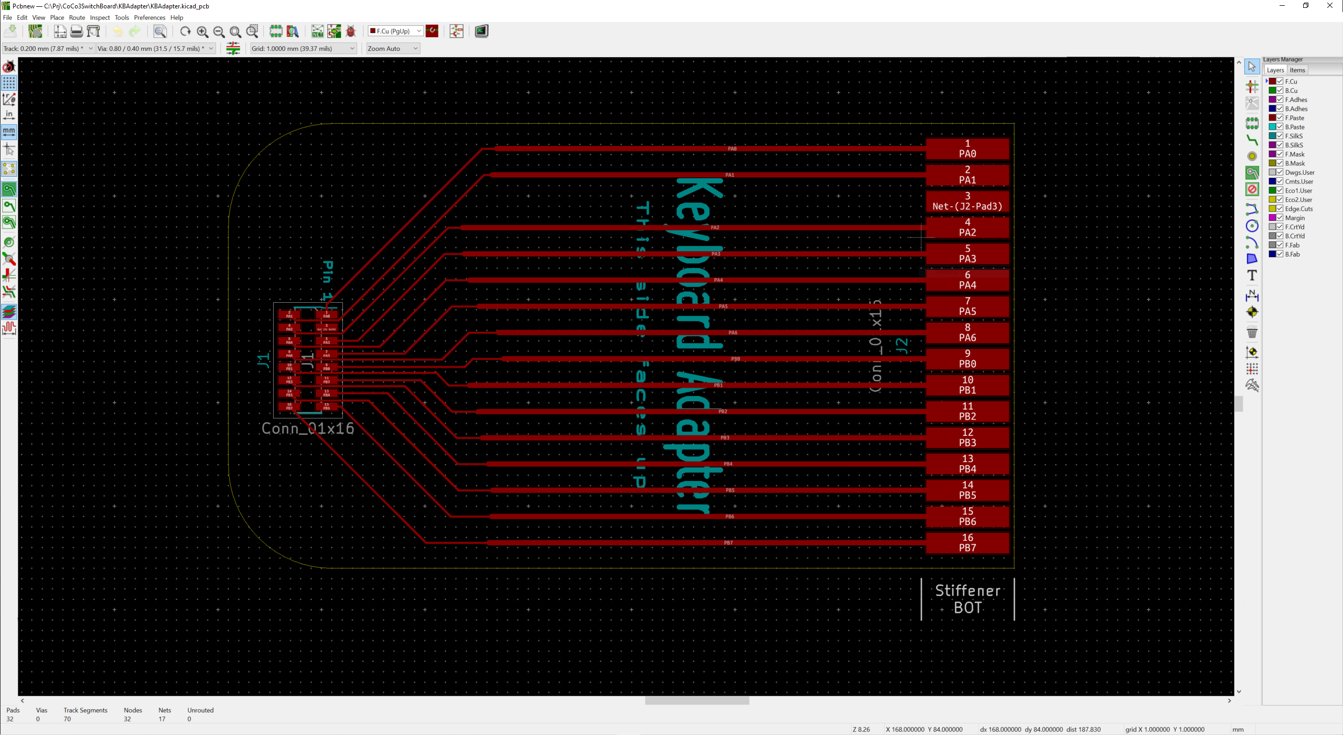
KBAdapter/Photos/Kicad-Adapter.PNG
