mrojas36/CoCoSwitchboard/Designs/Kailh Polia.step

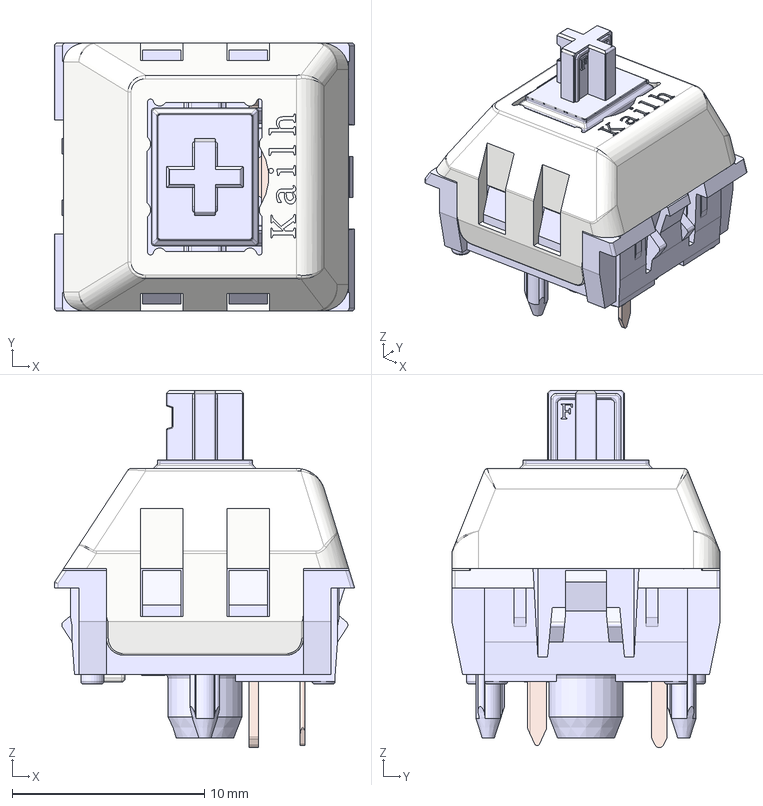
[picture p82: CAD file, 2022-09-06]
Designs/Kailh Polia.step
15.6 x 14.0 x 18.5 mm
Housing
ThickContact
SpringContact
Stem
Lid
