mrojas36/CoCoSwitchboard/EdgeAdapter/SSW-116-02-L-S-RA.step

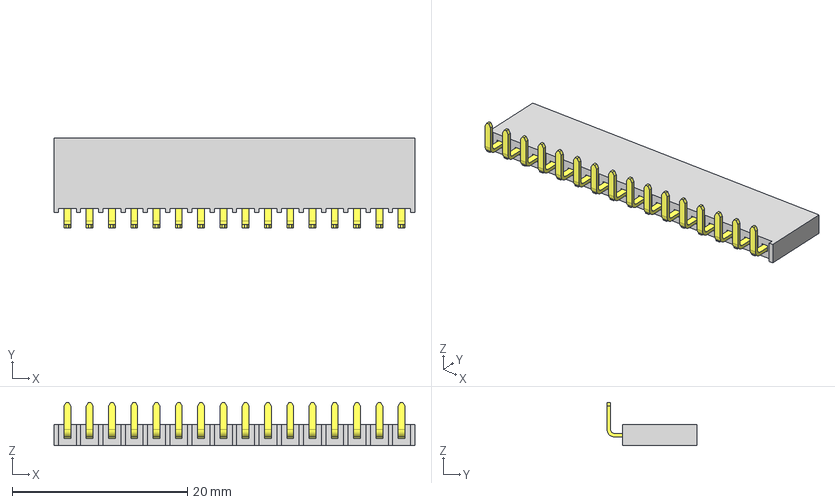
[picture p83: CAD file, 2023-02-24]
EdgeAdapter/SSW-116-02-L-S-RA.step
41.1 x 10.2 x 4.94 mm
P2SSW-116-02-L-S-RA
T1SSW-116-02-L-S-RA
