mrojas36/CoCoSwitchboard/CoCo1Switchboard/Objects/Post.stl

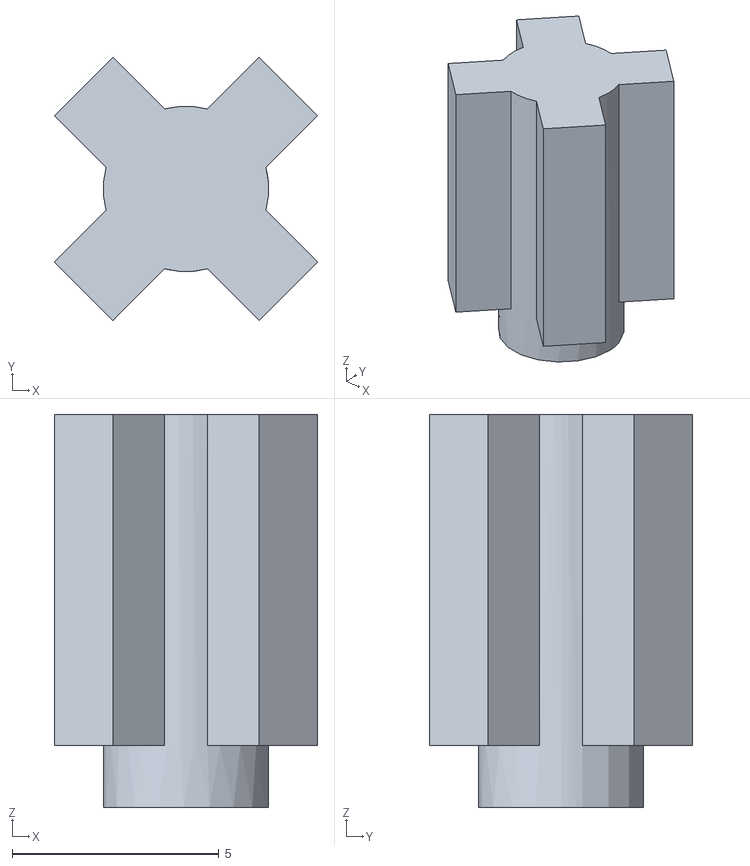
[picture p84: CAD file, 2022-08-15]
CoCo1Switchboard/Objects/Post.stl
6.36 x 6.36 x 9.50
