mrojas36/CoCoSwitchboard/CoCo2Switchboard/Objects/Coco2Spacer-Right.stl

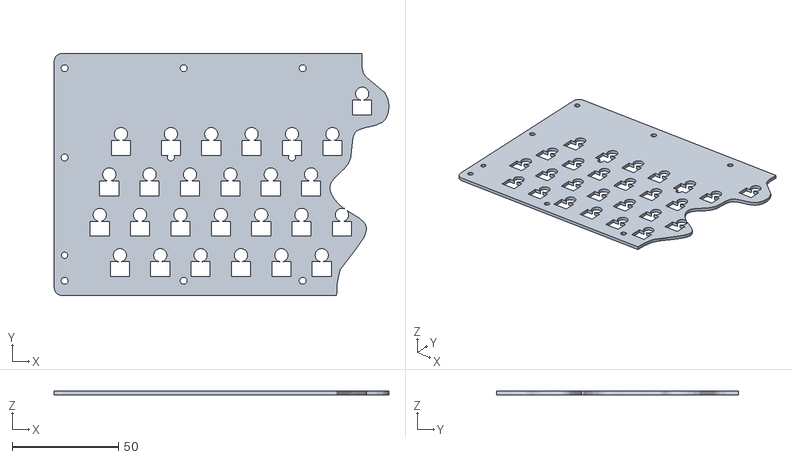
[picture p85: CAD file, 2022-09-06]
CoCo2Switchboard/Objects/Coco2Spacer-Right.stl
157.6 x 114.0 x 1.80
