mrojas36/CoCoSwitchboard/Designs/Kailh Hotswap.step

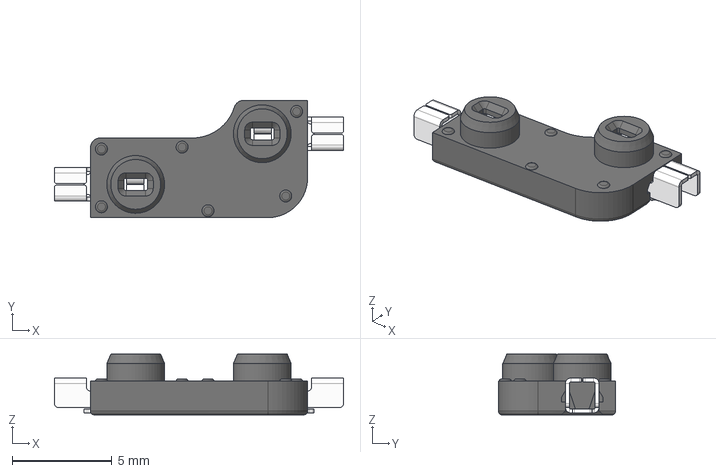
[picture p86: CAD file, 2022-09-06]
Designs/Kailh Hotswap.step
14.5 x 5.89 x 3.05 mm
Contact x 2
