mrojas36/CoCoSwitchboard/CoCo2Switchboard/Objects/Coco2SwitchJig.stl

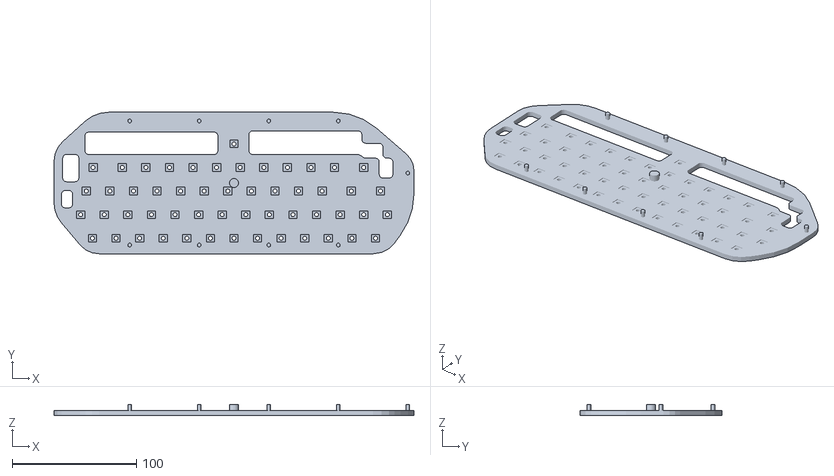
[picture p87: CAD file, 2022-08-15]
CoCo2Switchboard/Objects/Coco2SwitchJig.stl
290.0 x 114.0 x 9.00
