mrojas36/CoCoSwitchboard/CoCo3Switchboard/Objects/EVQQ2-Switch.stl

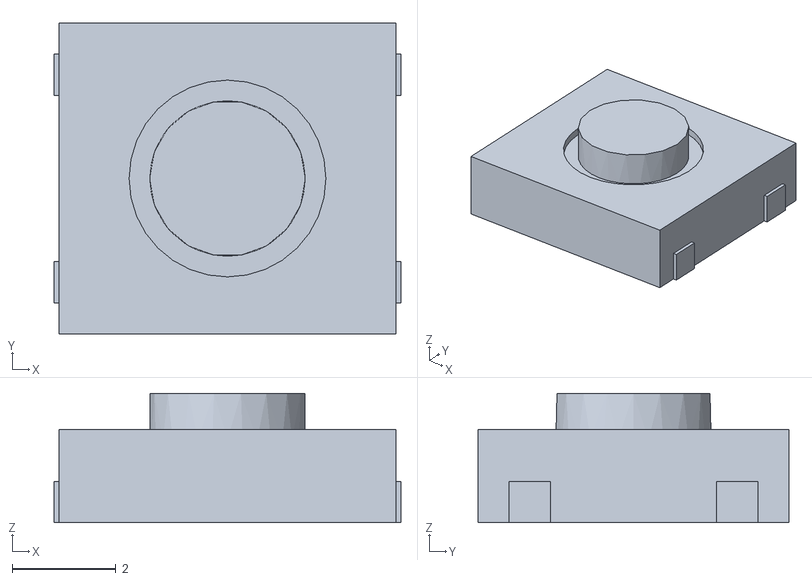
[picture p88: CAD file, 2022-08-15]
CoCo3Switchboard/Objects/EVQQ2-Switch.stl
6.70 x 6.00 x 2.50
