mrojas36/CoCoSwitchboard/CoCo1Switchboard/Objects/CoCo1-Right.stl

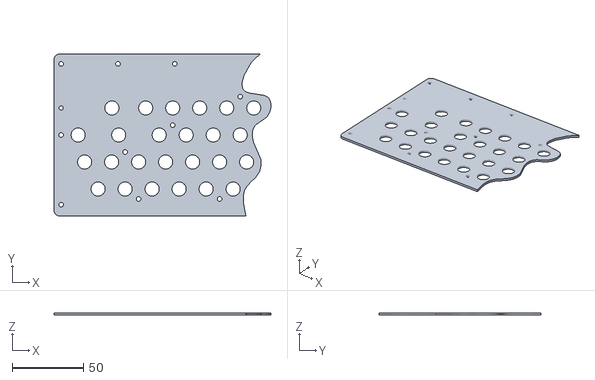
[picture p89: CAD file, 2022-08-15]
CoCo1Switchboard/Objects/CoCo1-Right.stl
152.6 x 114.0 x 1.70
