mrojas36/CoCoSwitchboard/CoCo3Switchboard/Objects/Coco3SwitchJig.stl

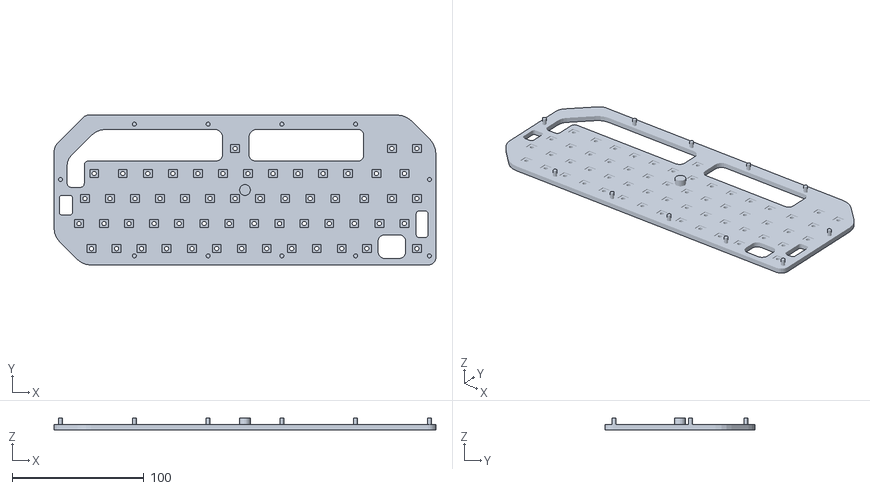
[picture p90: CAD file, 2022-08-15]
CoCo3Switchboard/Objects/Coco3SwitchJig.stl
290.0 x 114.0 x 9.00
