mrojas36/CoCoSwitchboard/CoCo1Switchboard/Objects/TestPanelLeft.stl

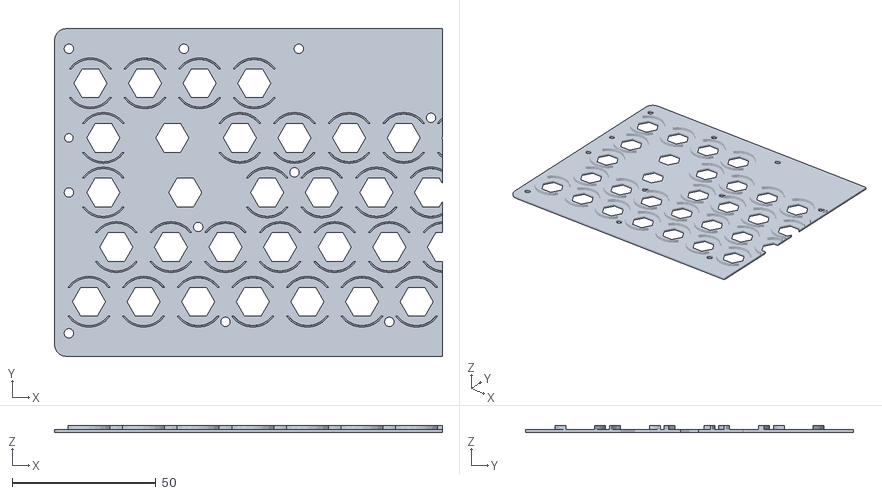
[picture p91: CAD file, 2022-08-15]
CoCo1Switchboard/Objects/TestPanelLeft.stl
135.0 x 114.0 x 2.50
