mrojas36/CoCoSwitchboard/CoCo3Switchboard/Objects/Coco3SwitchJig-Test.stl

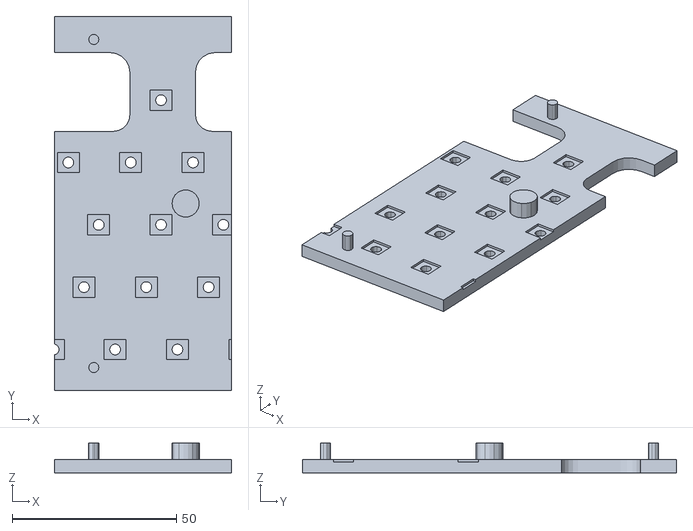
[picture p92: CAD file, 2022-08-15]
CoCo3Switchboard/Objects/Coco3SwitchJig-Test.stl
54.0 x 114.0 x 9.00
