mrojas36/CoCoSwitchboard/CoCo1Switchboard/Objects/TestPanelRight.stl

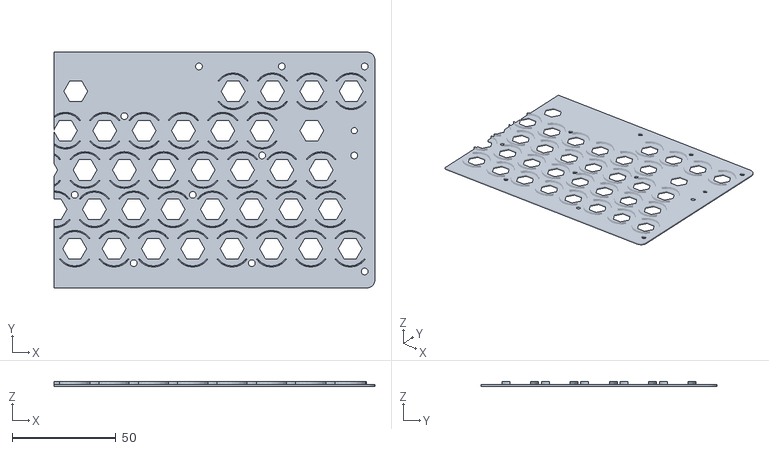
[picture p93: CAD file, 2022-08-15]
CoCo1Switchboard/Objects/TestPanelRight.stl
155.0 x 114.0 x 2.50
