mrojas36/CoCoSwitchboard/CoCo1Switchboard/Objects/TestPost.stl

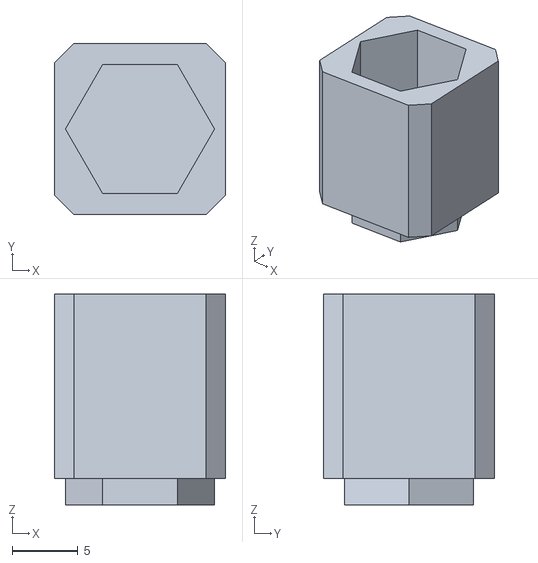
[picture p94: CAD file, 2022-08-15]
CoCo1Switchboard/Objects/TestPost.stl
13.0 x 13.0 x 16.0
